Acidjeremy07/Monitoreo-Ambystomas-Arduino/Datasheet's/Referencia esp01.png

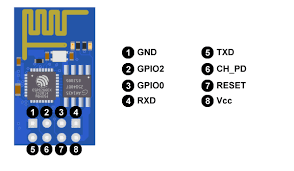
Datasheet's/Referencia esp01.png
