Acidjeremy07/Monitoreo-Ambystomas-Arduino/Expo TT1/Imagenes objetivos especificos/Gabinete de arduino.webp

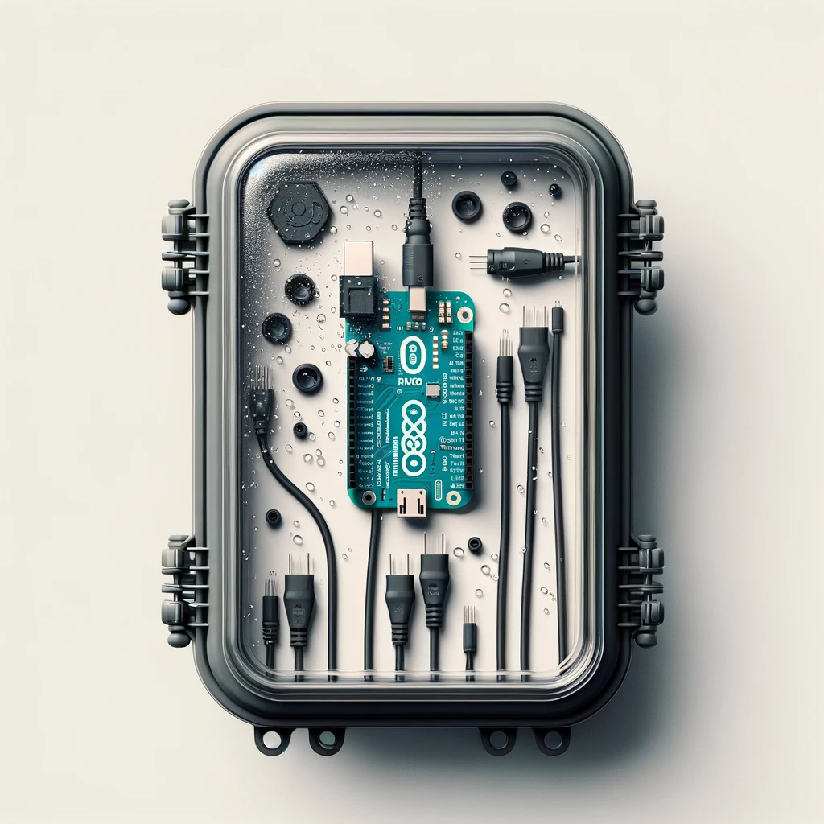
Expo TT1/Imagenes objetivos especificos/Gabinete de arduino.webp
