Acidjeremy07/Monitoreo-Ambystomas-Arduino/Expo TT1/Imagenes objetivos especificos/Sistema de alerta de ajolotes.jpg

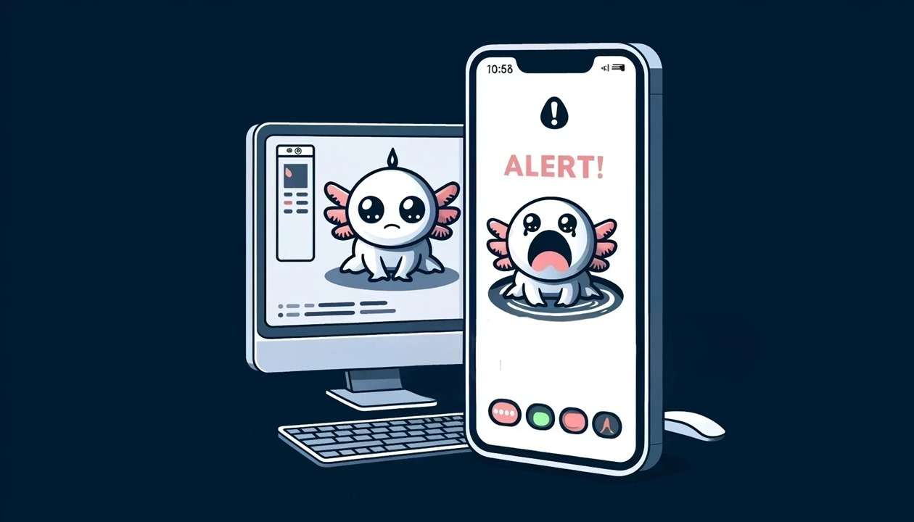
Expo TT1/Imagenes objetivos especificos/Sistema de alerta de ajolotes.jpg
