Acidjeremy07/Monitoreo-Ambystomas-Arduino/Expo TT1/Imagenes objetivos especificos/Sistema web progresivo.webp

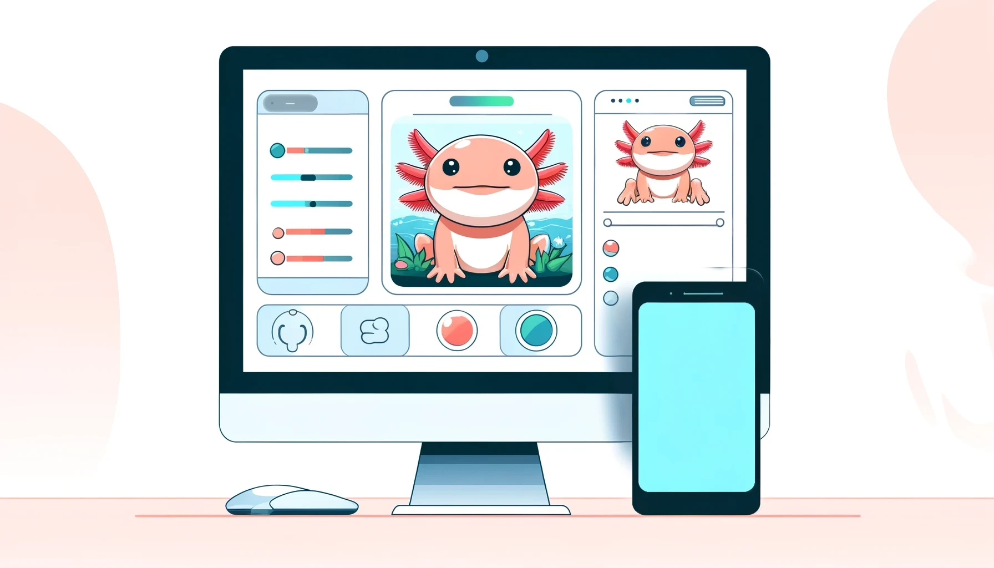
Expo TT1/Imagenes objetivos especificos/Sistema web progresivo.webp
