Acidjeremy07/Monitoreo-Ambystomas-Arduino/Expo TT1/PNG Ajolotes/Ajolotes a la derecha.png

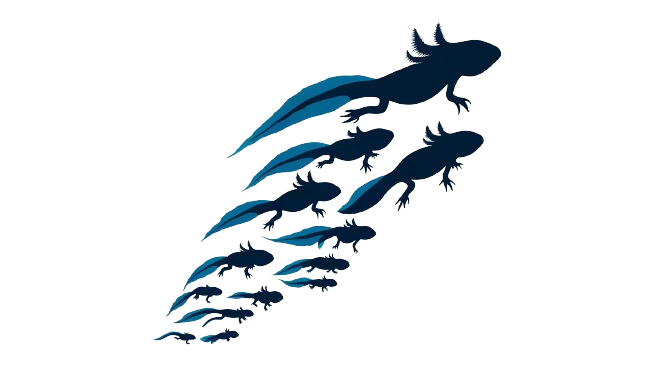
Expo TT1/PNG Ajolotes/Ajolotes a la derecha.png
