Acidjeremy07/Monitoreo-Ambystomas-Arduino/Expo TT1/PNG Ajolotes/Ajolotes bebé.png

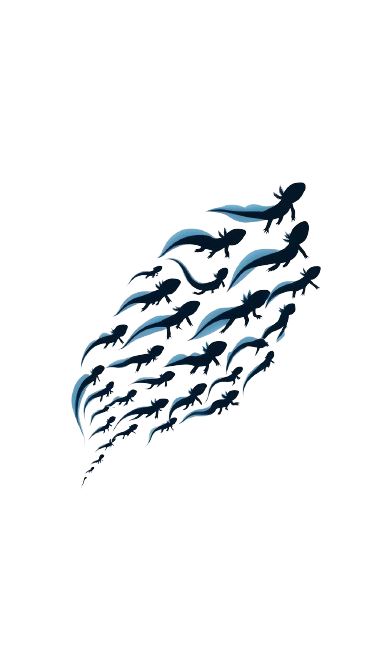
Expo TT1/PNG Ajolotes/Ajolotes bebé.png
