Acidjeremy07/Monitoreo-Ambystomas-Arduino/Expo TT1/PNG Ajolotes/Ajolotes grandes.png

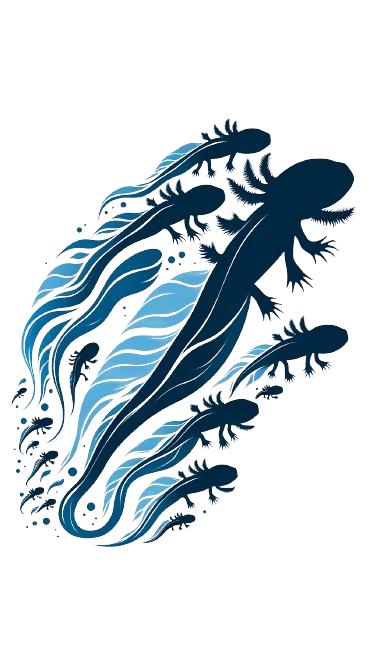
Expo TT1/PNG Ajolotes/Ajolotes grandes.png
