Acidjeremy07/Monitoreo-Ambystomas-Arduino/Expo TT1/PNG Ajolotes/Ajolotes viendo izq.png

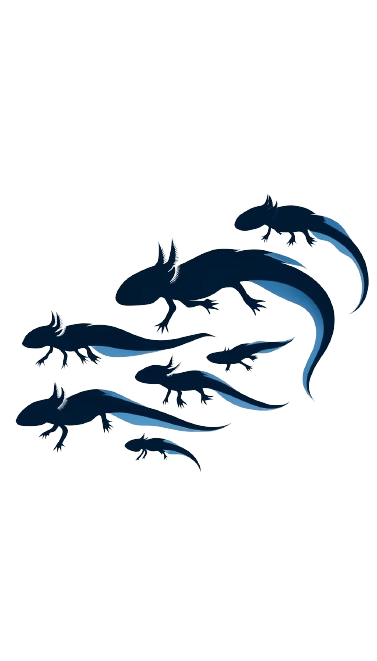
Expo TT1/PNG Ajolotes/Ajolotes viendo izq.png
