Acidjeremy07/Monitoreo-Ambystomas-Arduino/Expo TT1/PNG Ajolotes/Pecera de ajolotes PNG.png

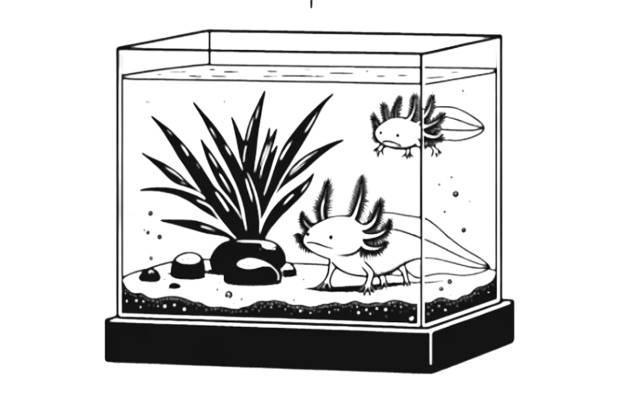
Expo TT1/PNG Ajolotes/Pecera de ajolotes PNG.png
