Acidjeremy07/Monitoreo-Ambystomas-Arduino/Expo TT1/PNG Ajolotes/Varios ajolotes.png

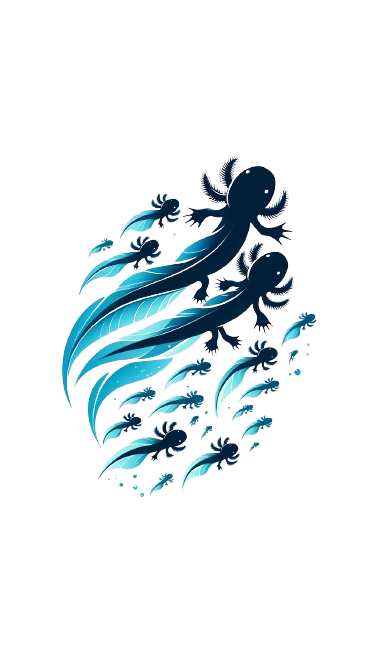
Expo TT1/PNG Ajolotes/Varios ajolotes.png
