Acidjeremy07/Monitoreo-Ambystomas-Arduino/PCB/TT Ambystoma v10 w-logo.PDF

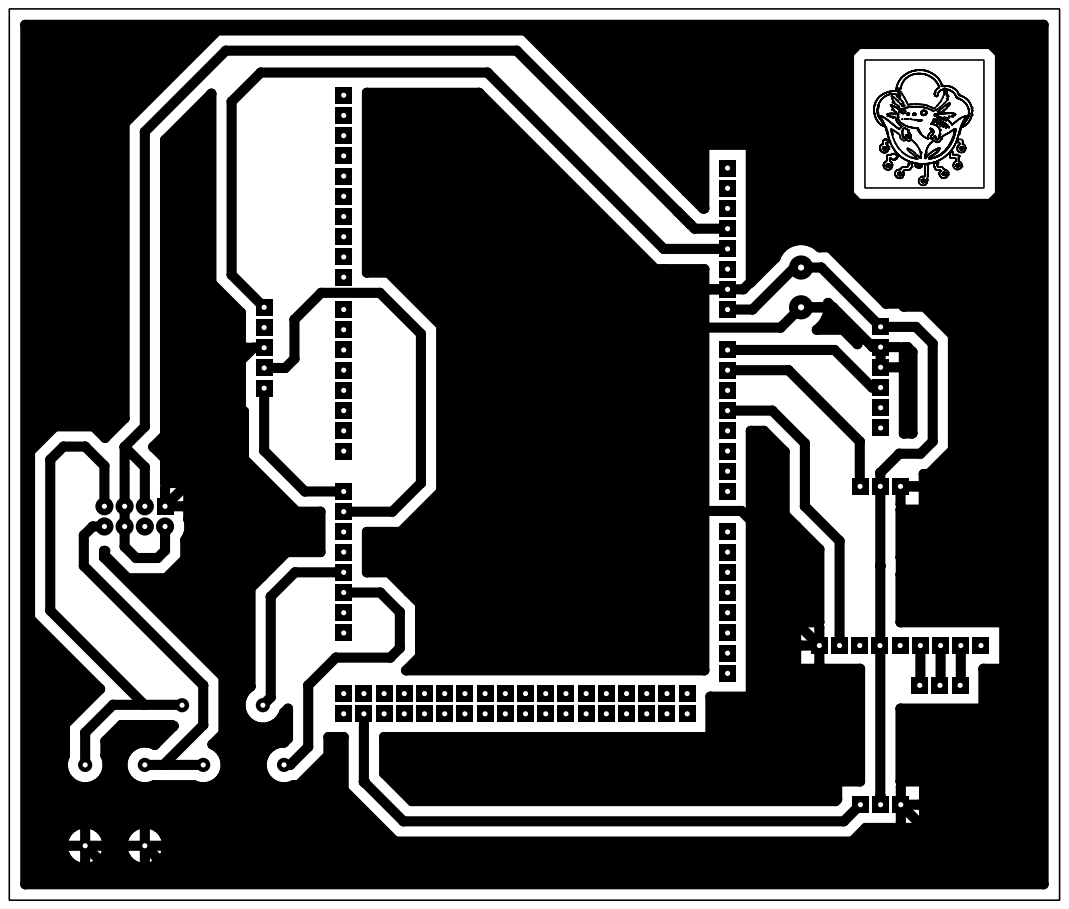
[picture p62: page 1]
