Acidjeremy07/Monitoreo-Ambystomas-Arduino/PCB/TT Ambystoma v5 w-logo imprimir varios.PDF

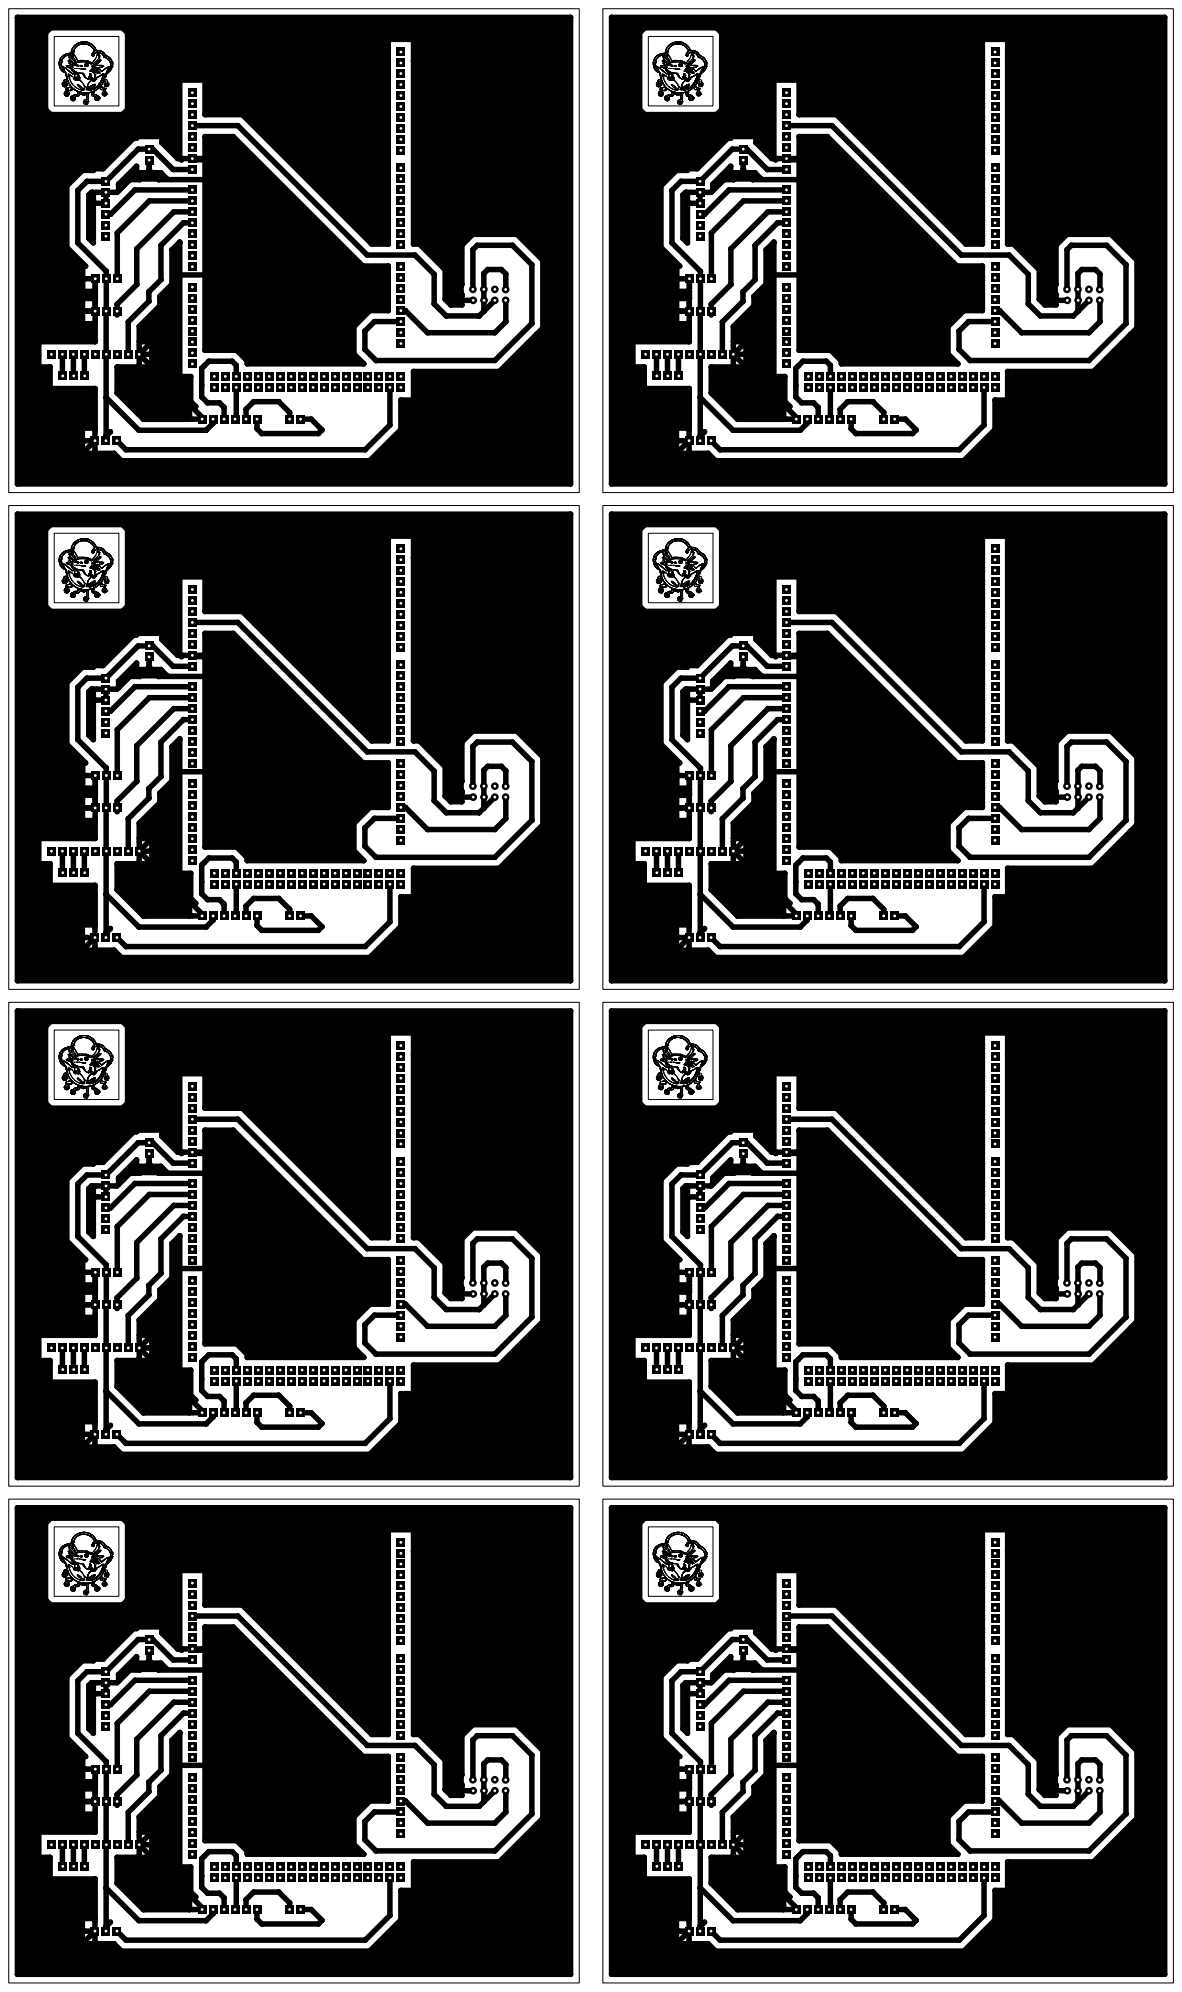
[picture p63: page 1]
