Acidjeremy07/Monitoreo-Ambystomas-Arduino/PCB/PDF imprimir/TT Ambystoma v3.2 w-logo.PDF

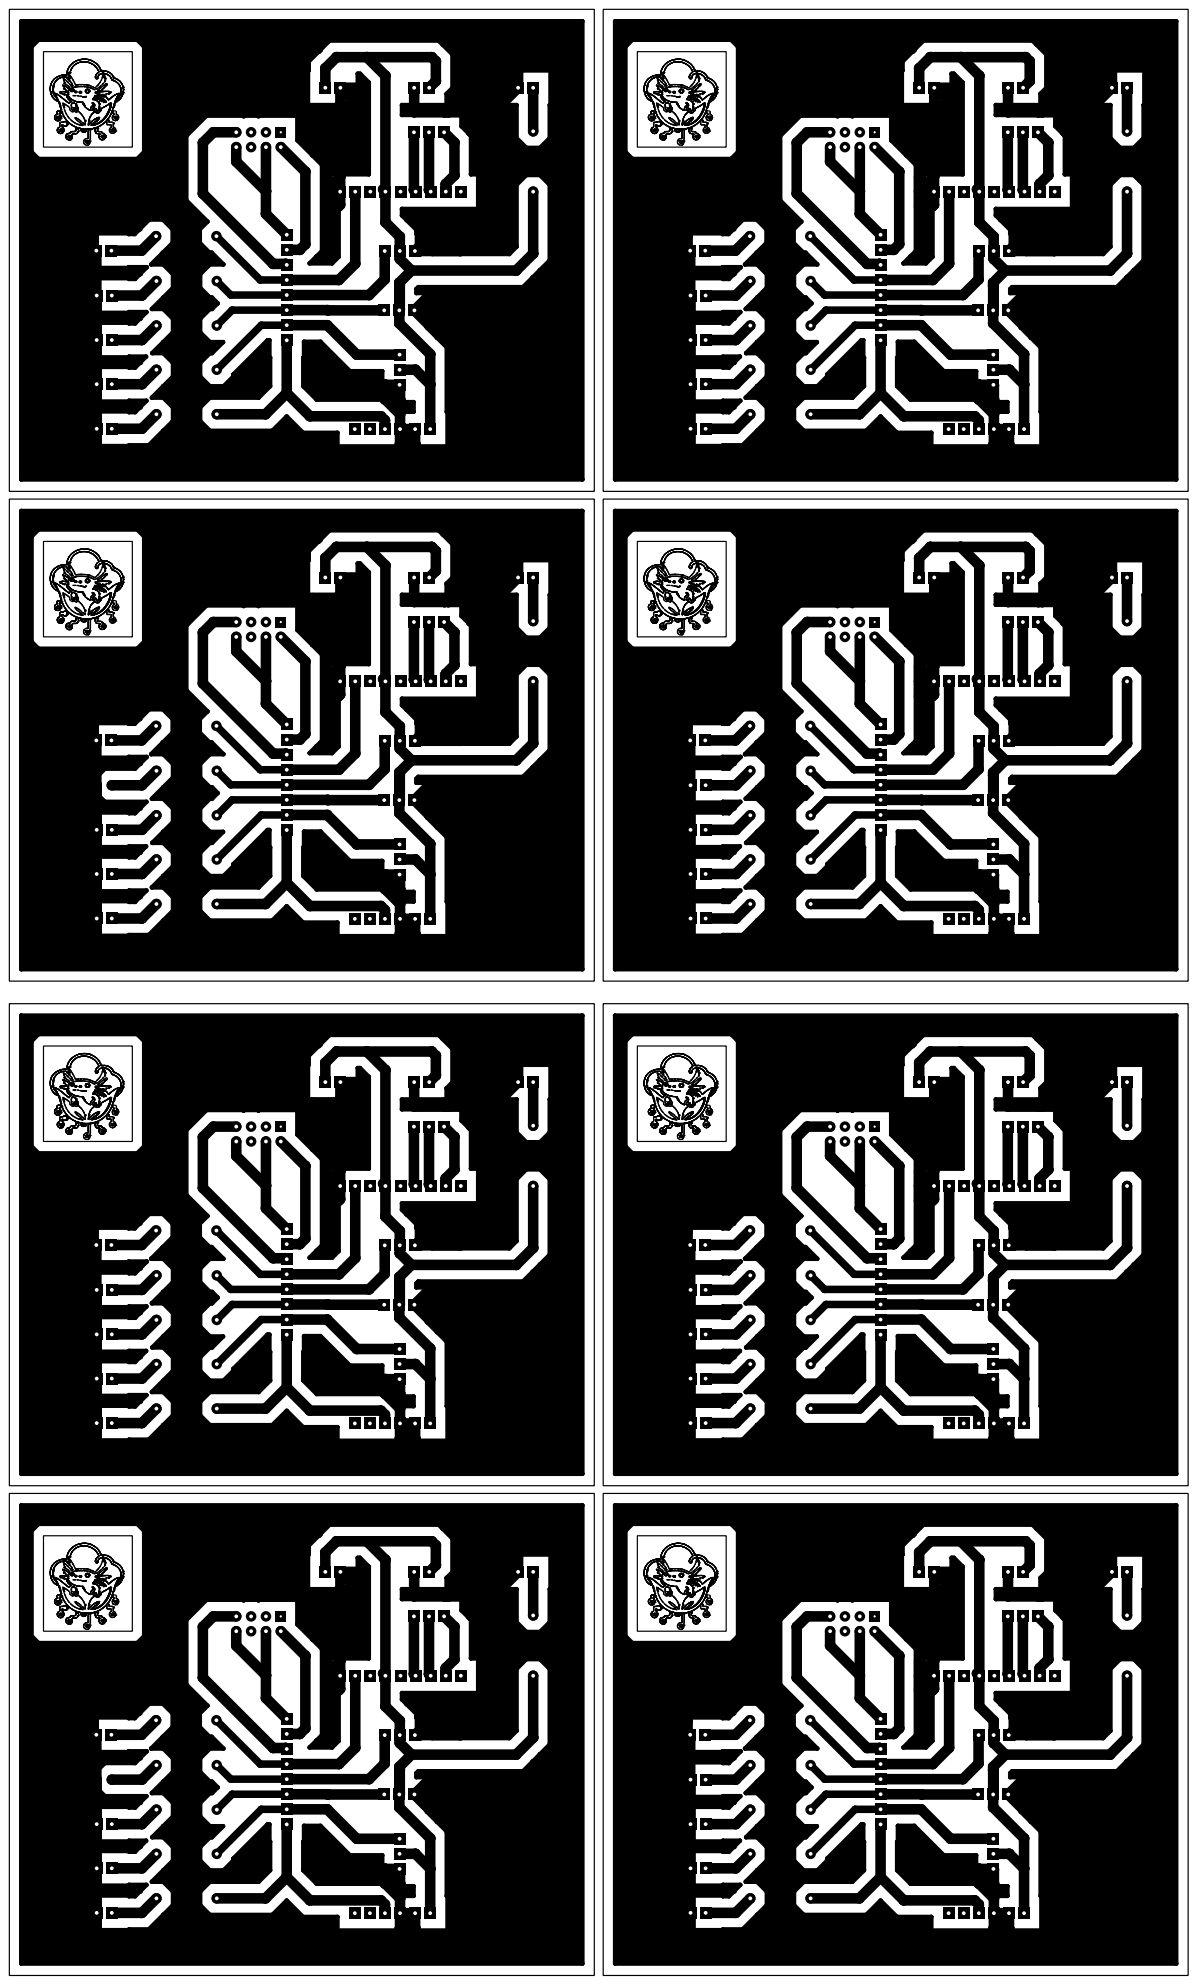
[picture p64: page 1]
