Acidjeremy07/Monitoreo-Ambystomas-Arduino/PCB/PDF imprimir/TT Ambystoma v3.PDF

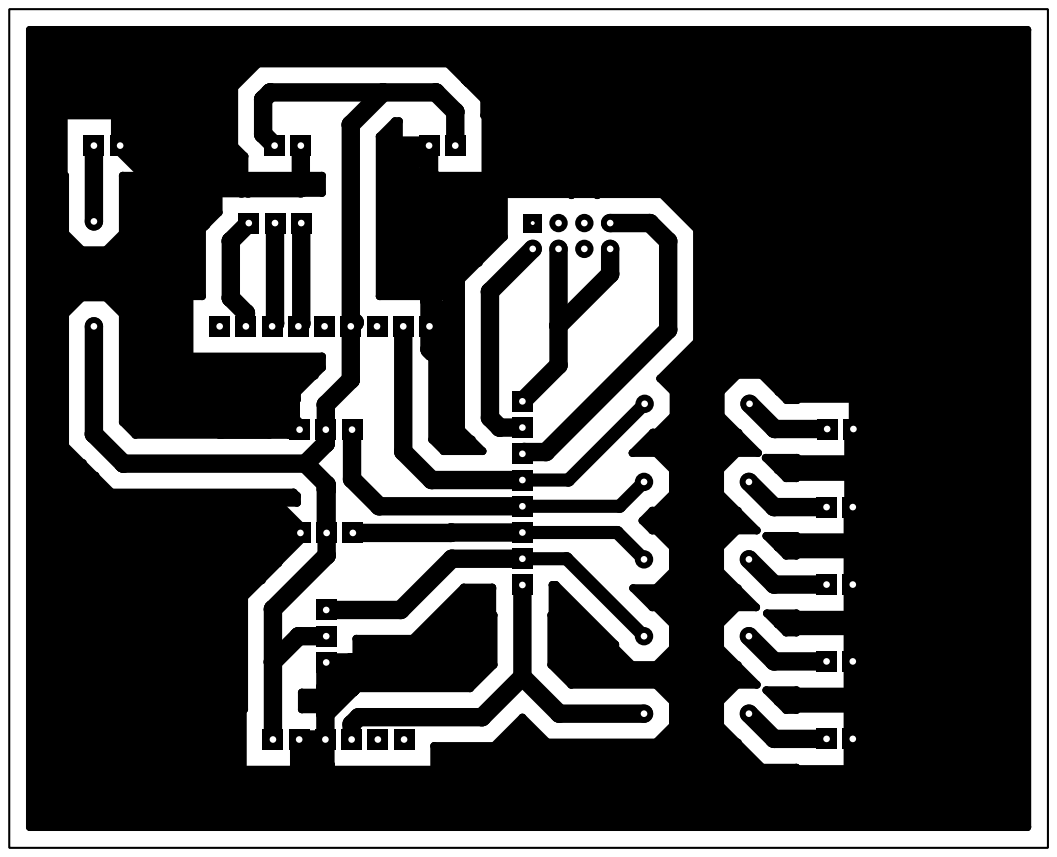
[picture p65: page 1]
