Acidjeremy07/Monitoreo-Ambystomas-Arduino/PCB/PDF imprimir/TT Ambystoma v2 X.PDF

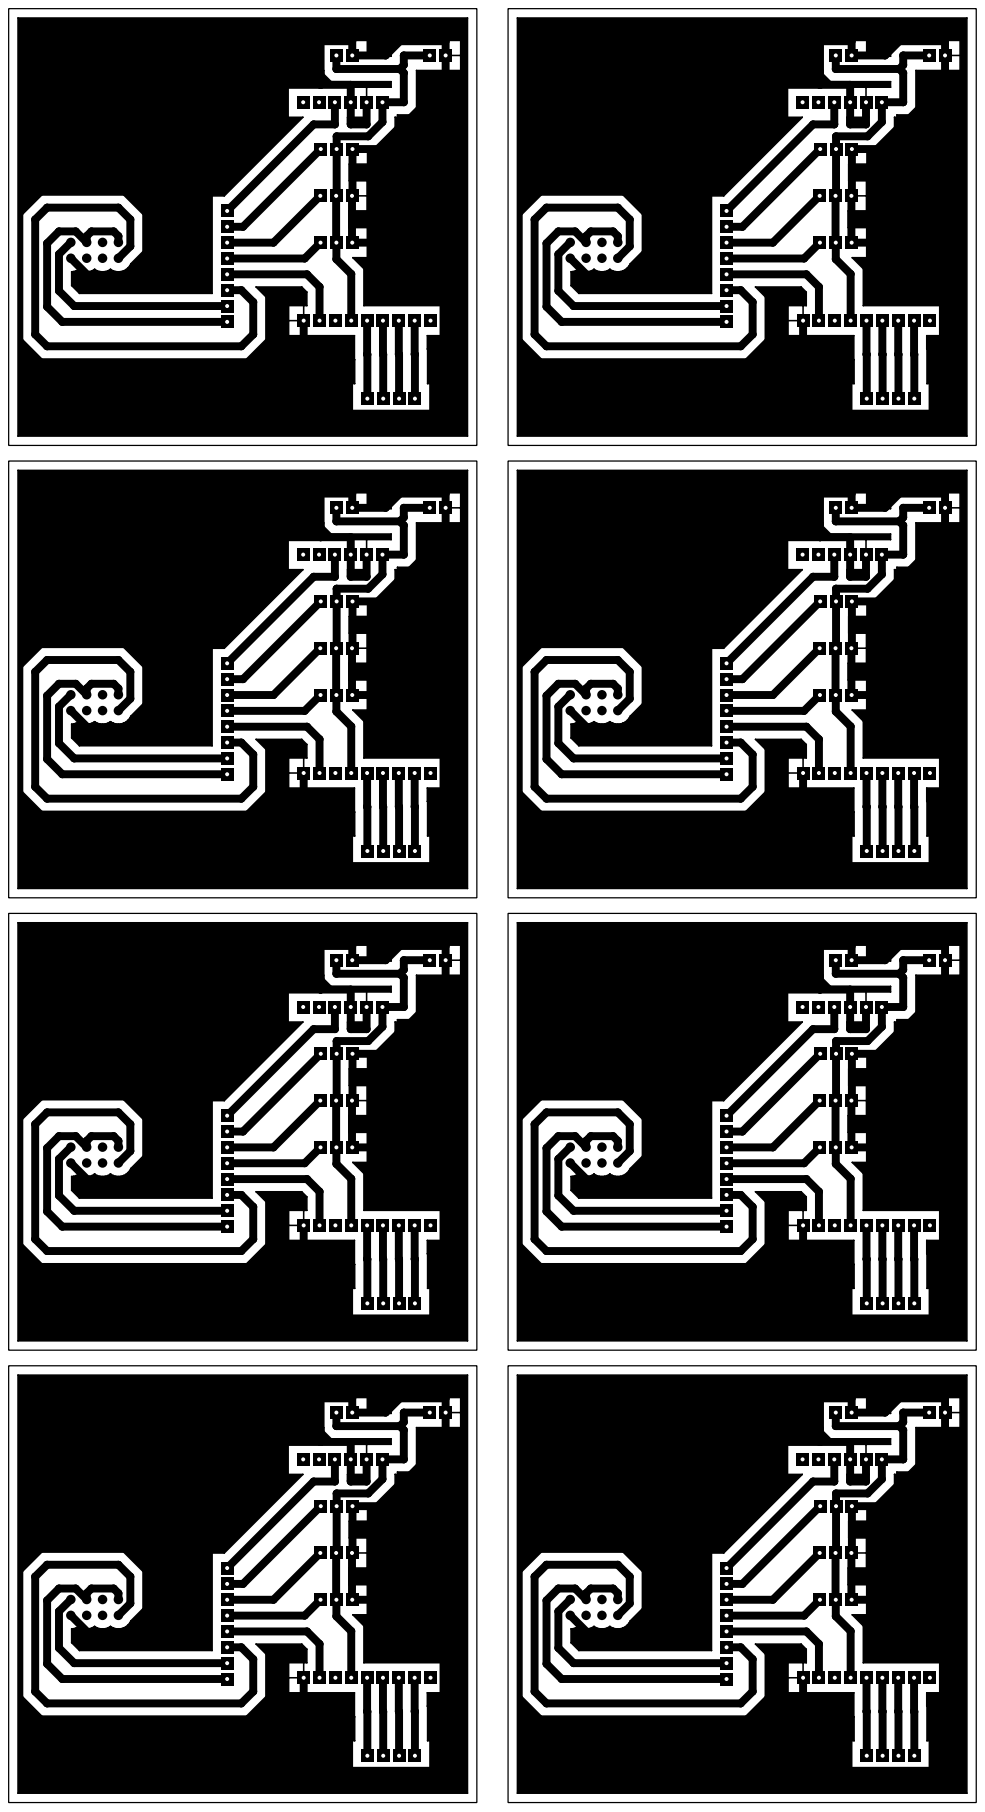
[picture p66: page 1]
