Acidjeremy07/Monitoreo-Ambystomas-Arduino/PCB/tt-v5.PDF

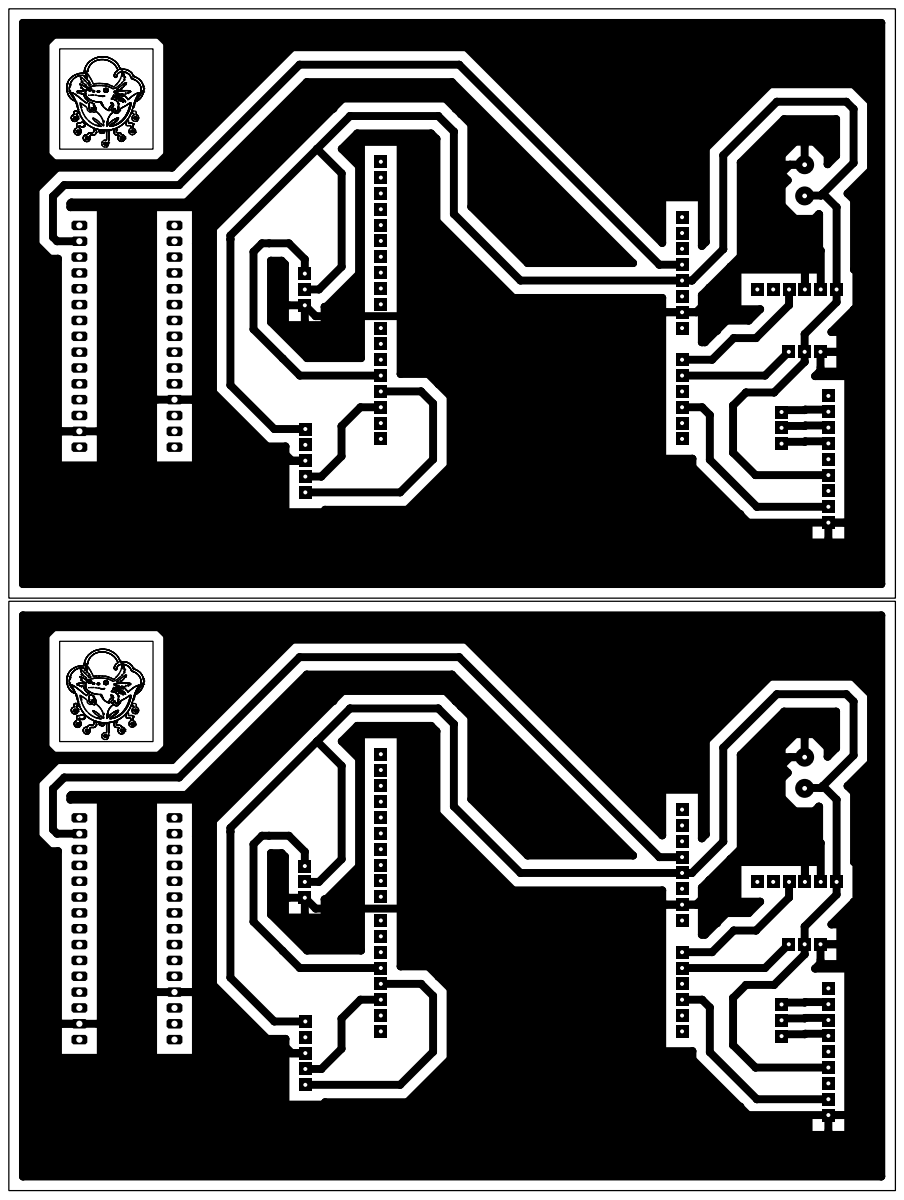
[picture p67: page 1]
