Acidjeremy07/Monitoreo-Ambystomas-Arduino/PCB/TT-V11.PDF

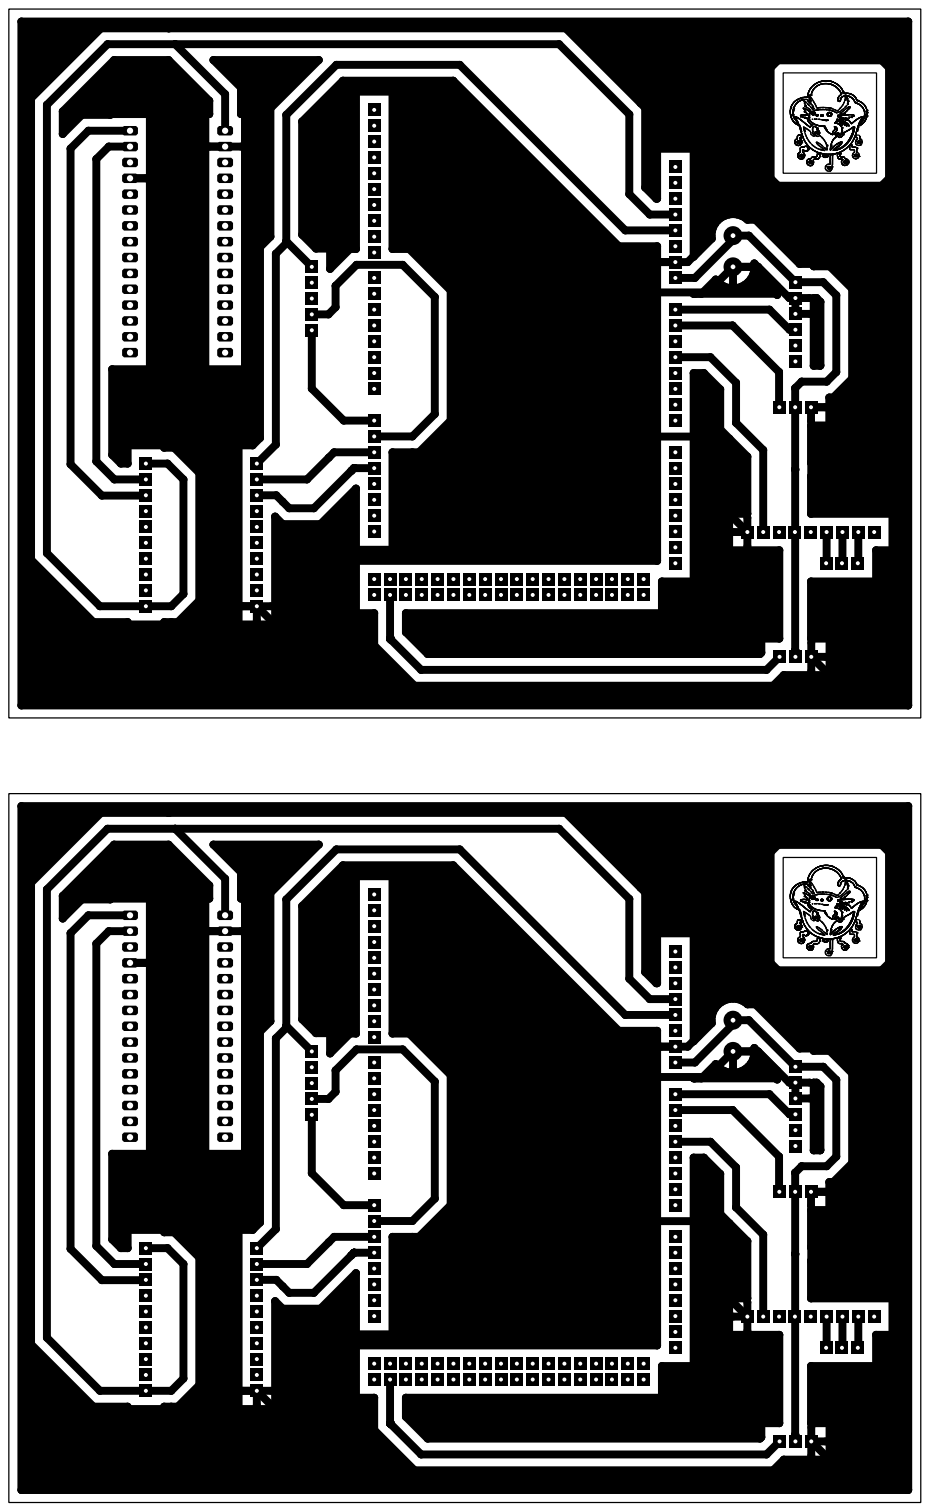
[picture p68: page 1]
