Acidjeremy07/Monitoreo-Ambystomas-Arduino/PCB/tt-v12.PDF

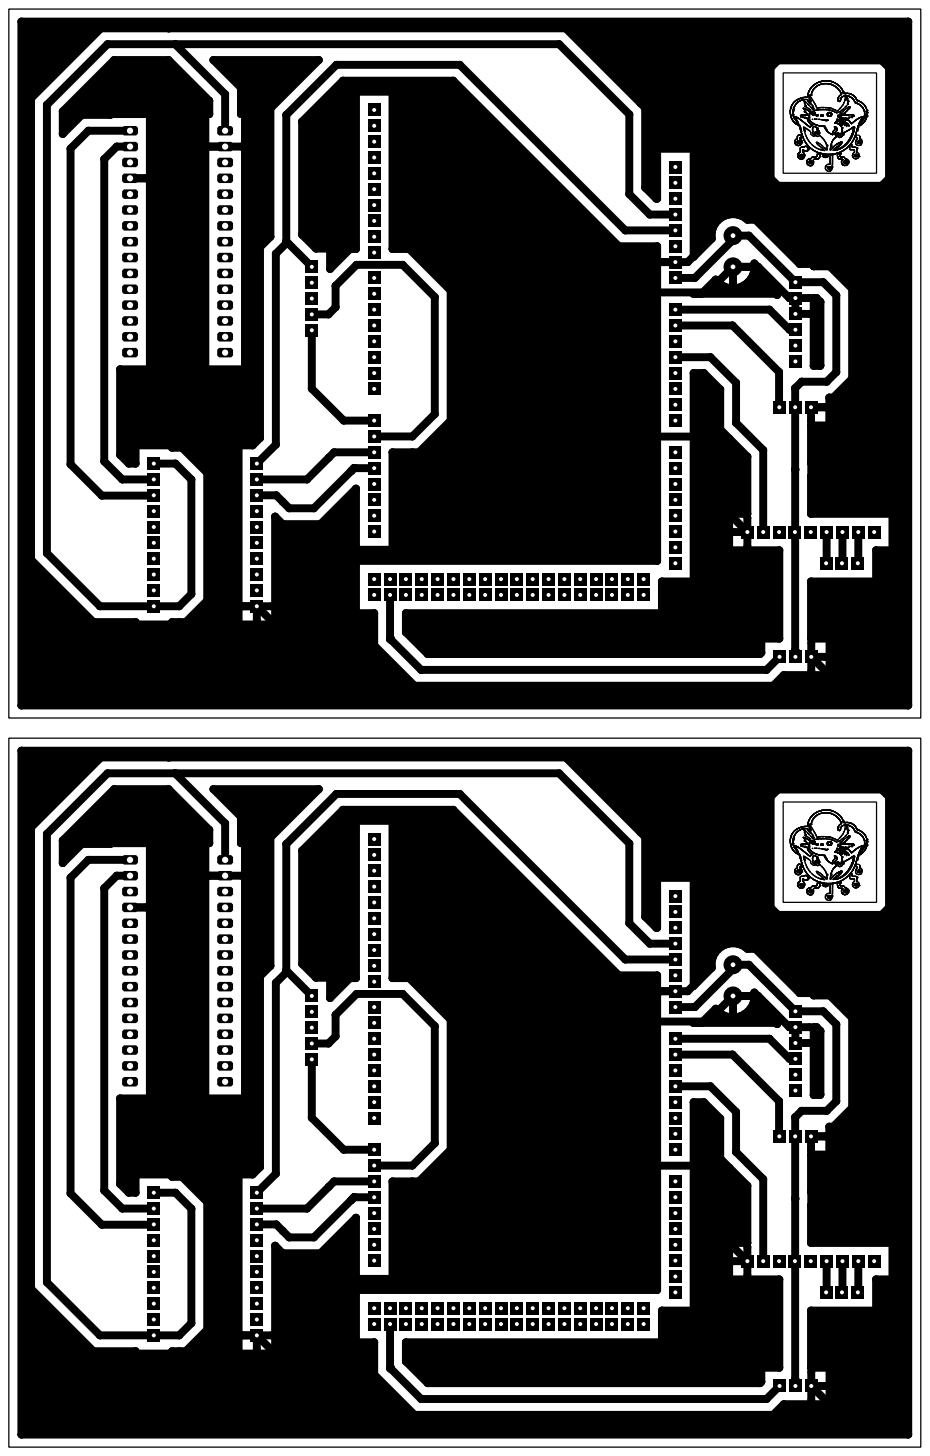
[picture p69: page 1]
