Acidjeremy07/Monitoreo-Ambystomas-Arduino/PCB/tt-v13.PDF

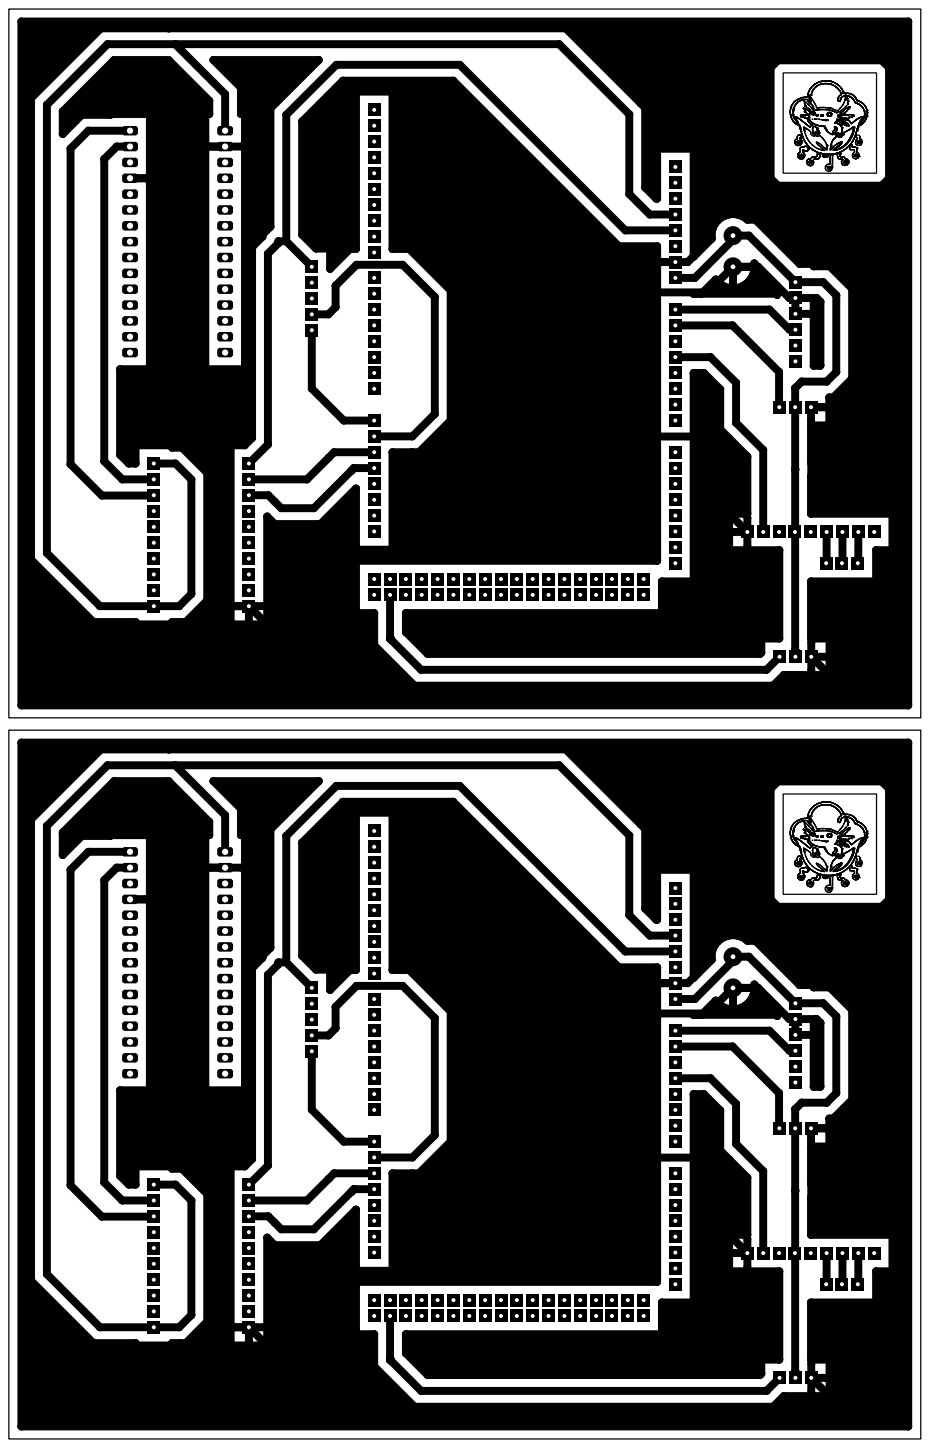
[picture p70: page 1]
