Acidjeremy07/Monitoreo-Ambystomas-Arduino/PCB/TT Ambystoma uno  w-logo.PDF

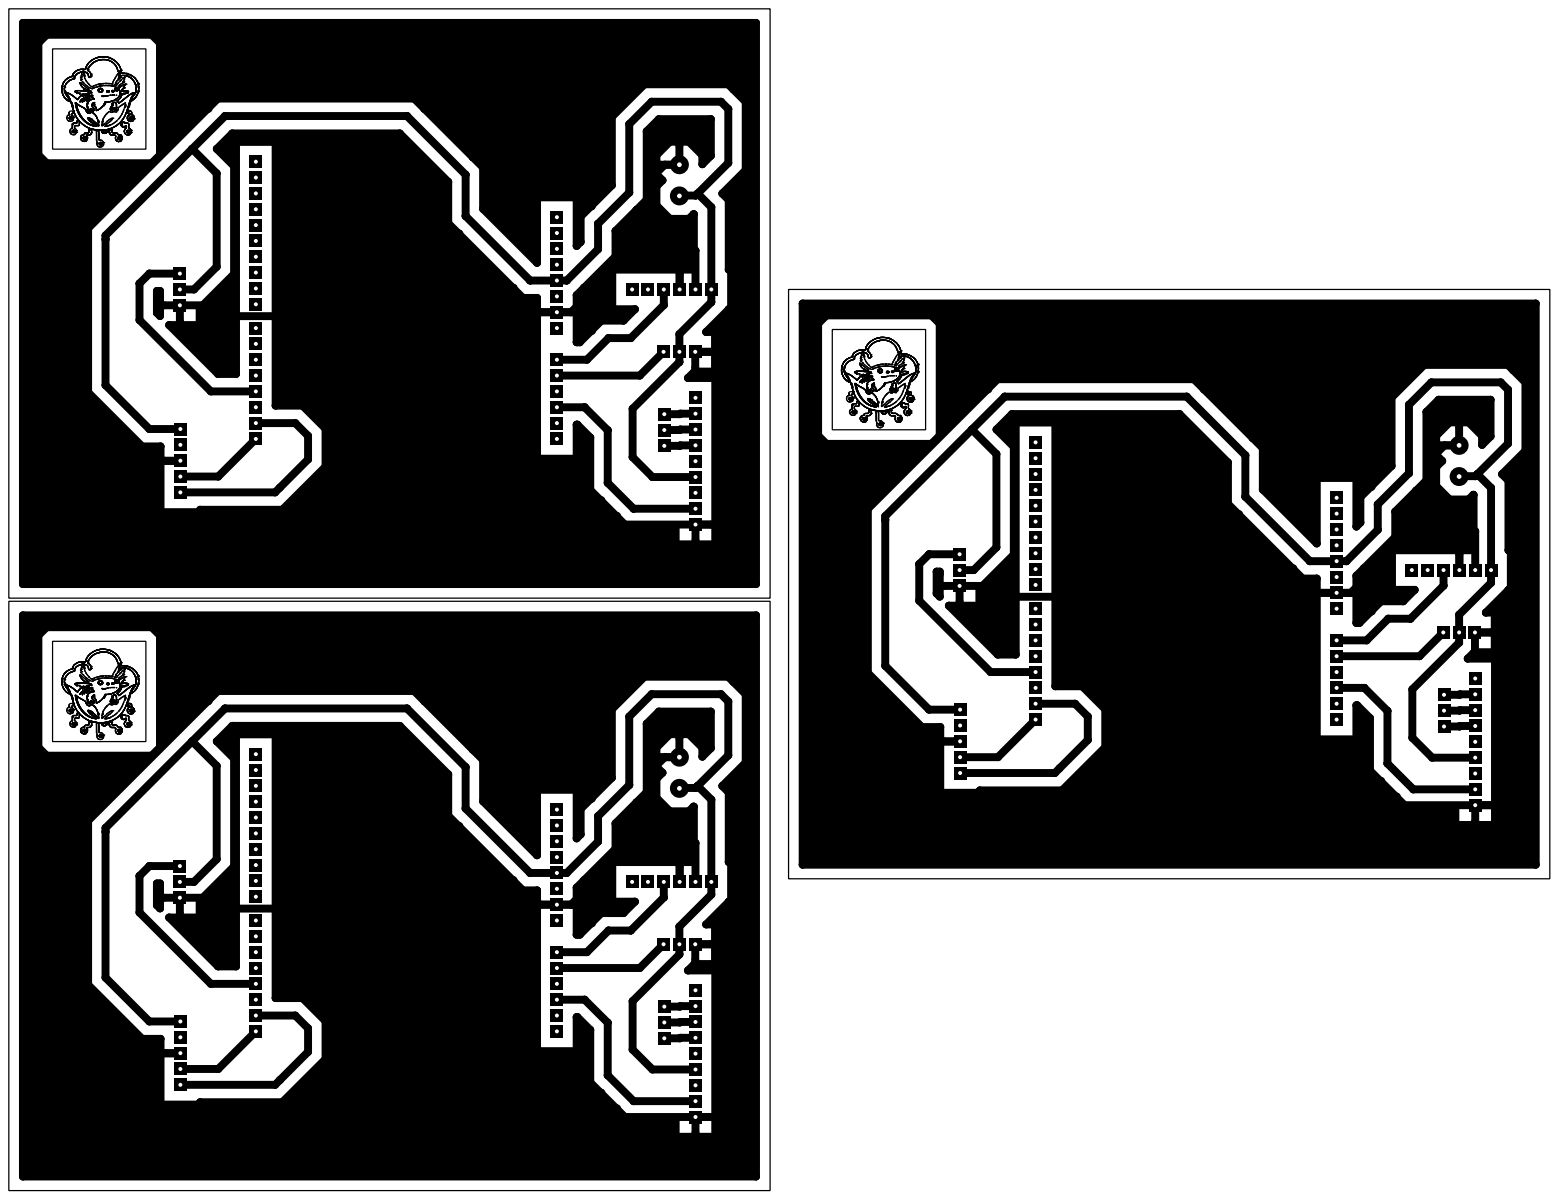
[picture p71: page 1]
