Acidjeremy07/Monitoreo-Ambystomas-Arduino/PCB/tt-v10.PDF

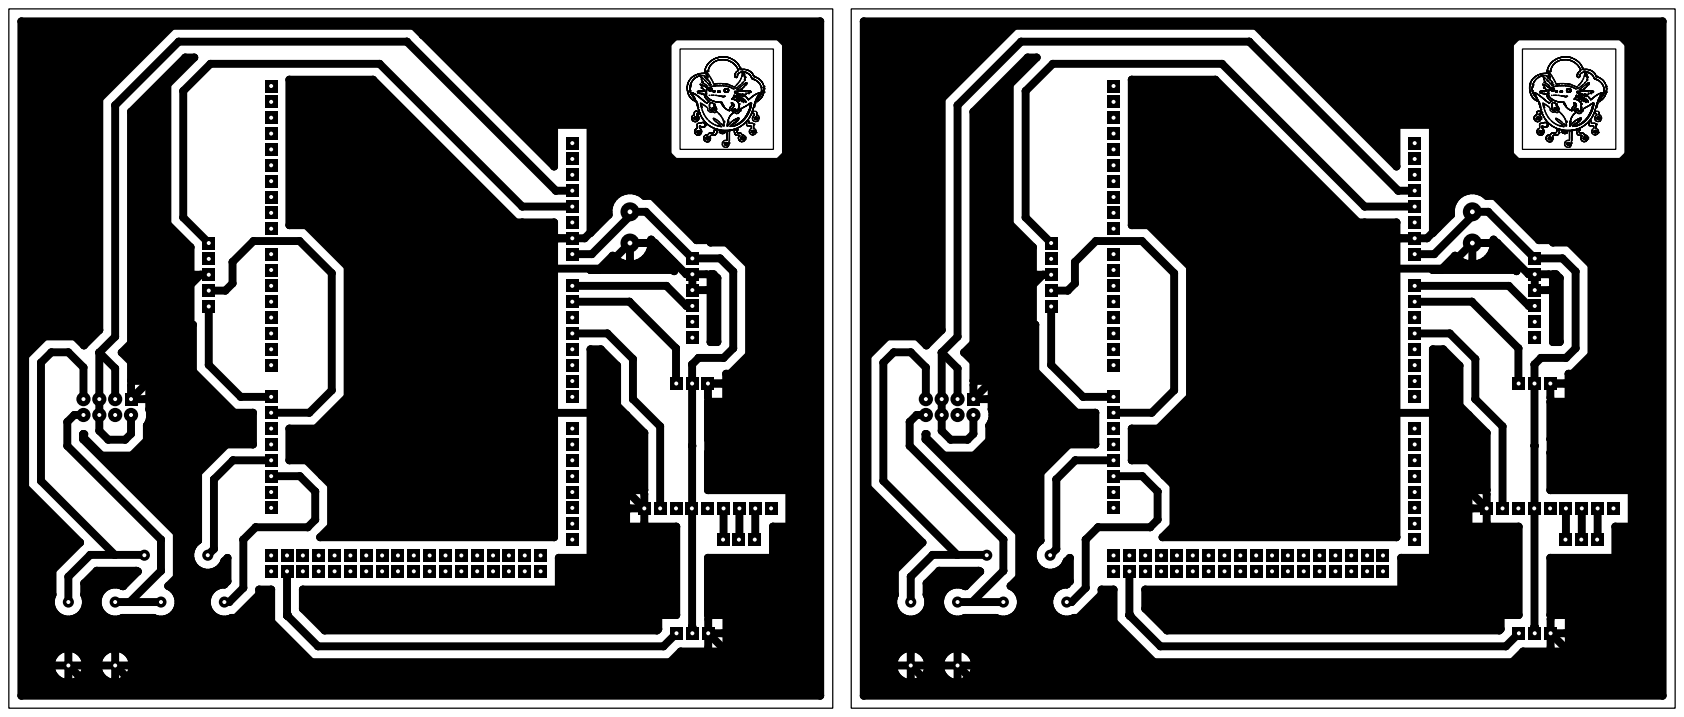
[picture p72: page 1]
