Acidjeremy07/Monitoreo-Ambystomas-Arduino/PCB/TT Ambystoma v8 w-logo.PDF

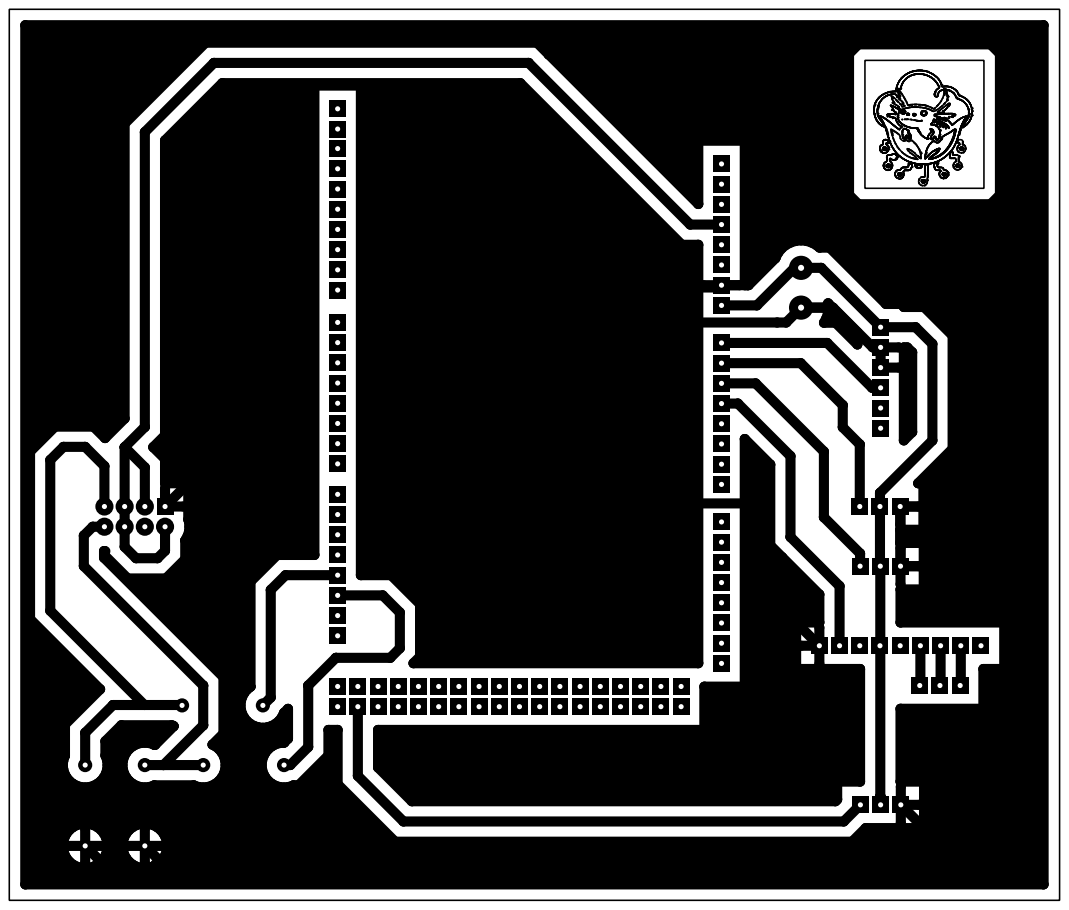
[picture p73: page 1]
