Acidjeremy07/Monitoreo-Ambystomas-Arduino/PCB/TT-V8.PDF

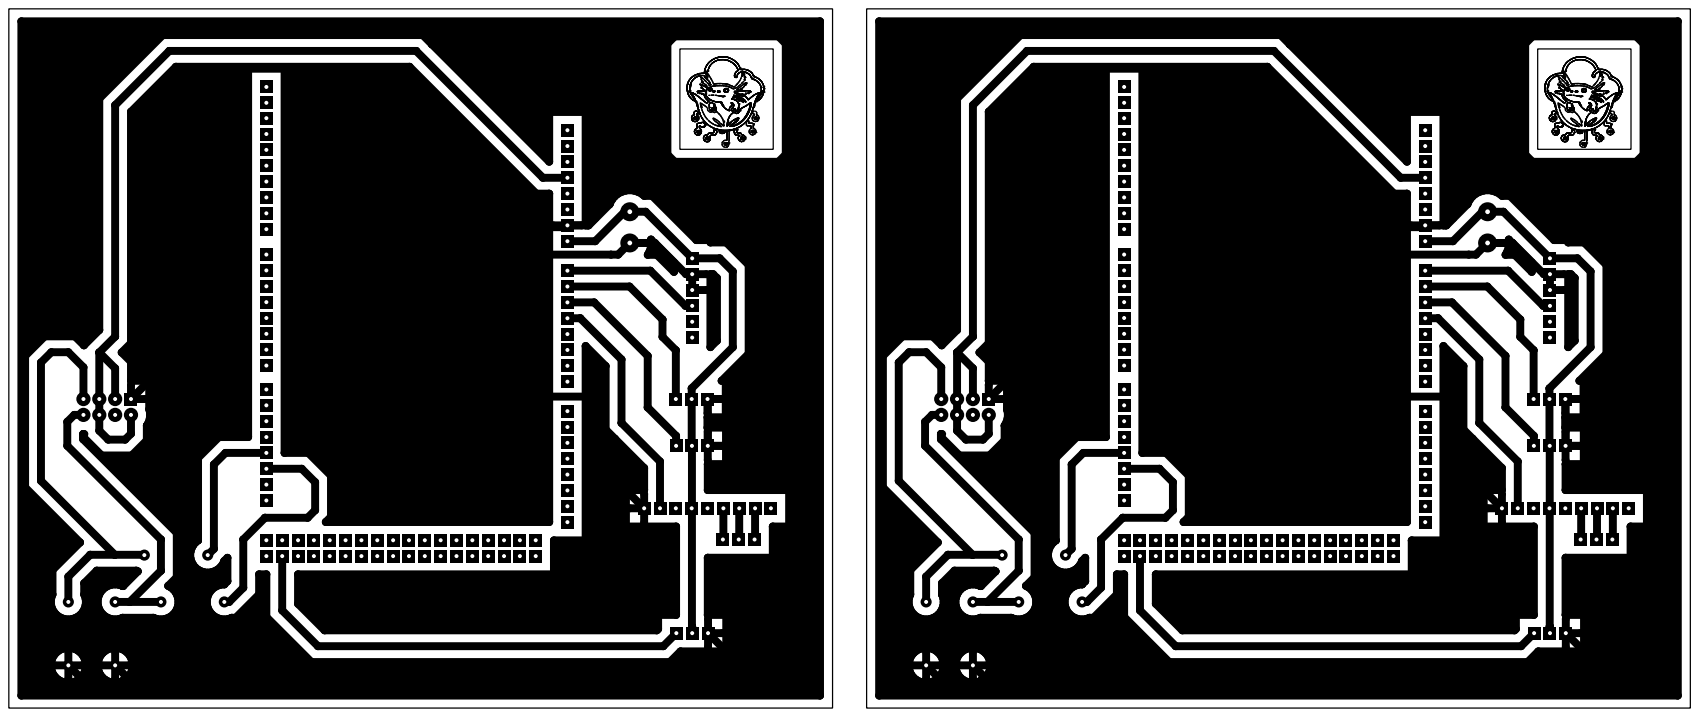
[picture p74: page 1]
