Acidjeremy07/Monitoreo-Ambystomas-Arduino/PCB/tt-v9.PDF

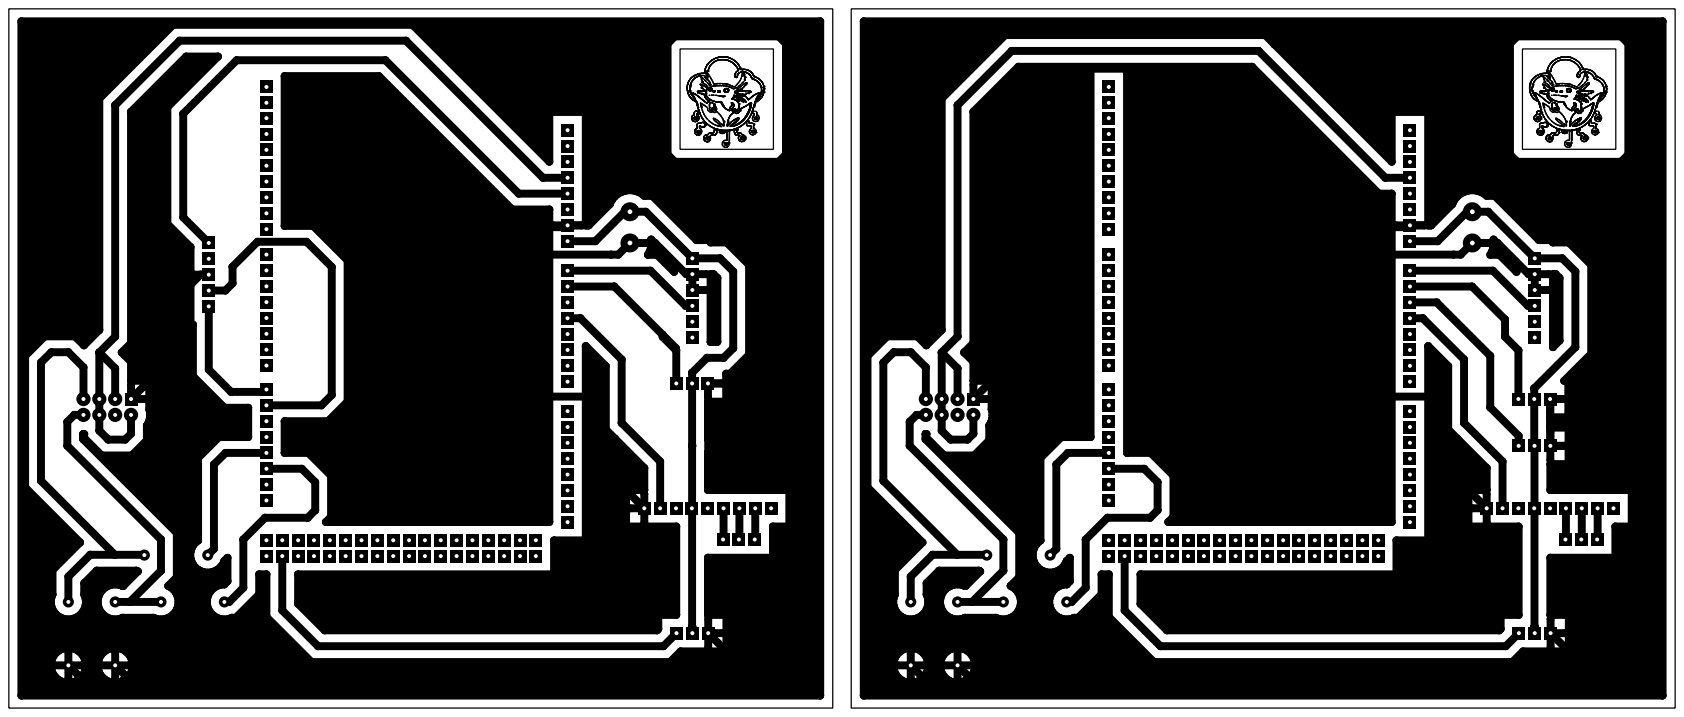
[picture p75: page 1]
