Acidjeremy07/Monitoreo-Ambystomas-Arduino/PCB/TT Ambystoma v4 w-logo imprimir varios.PDF

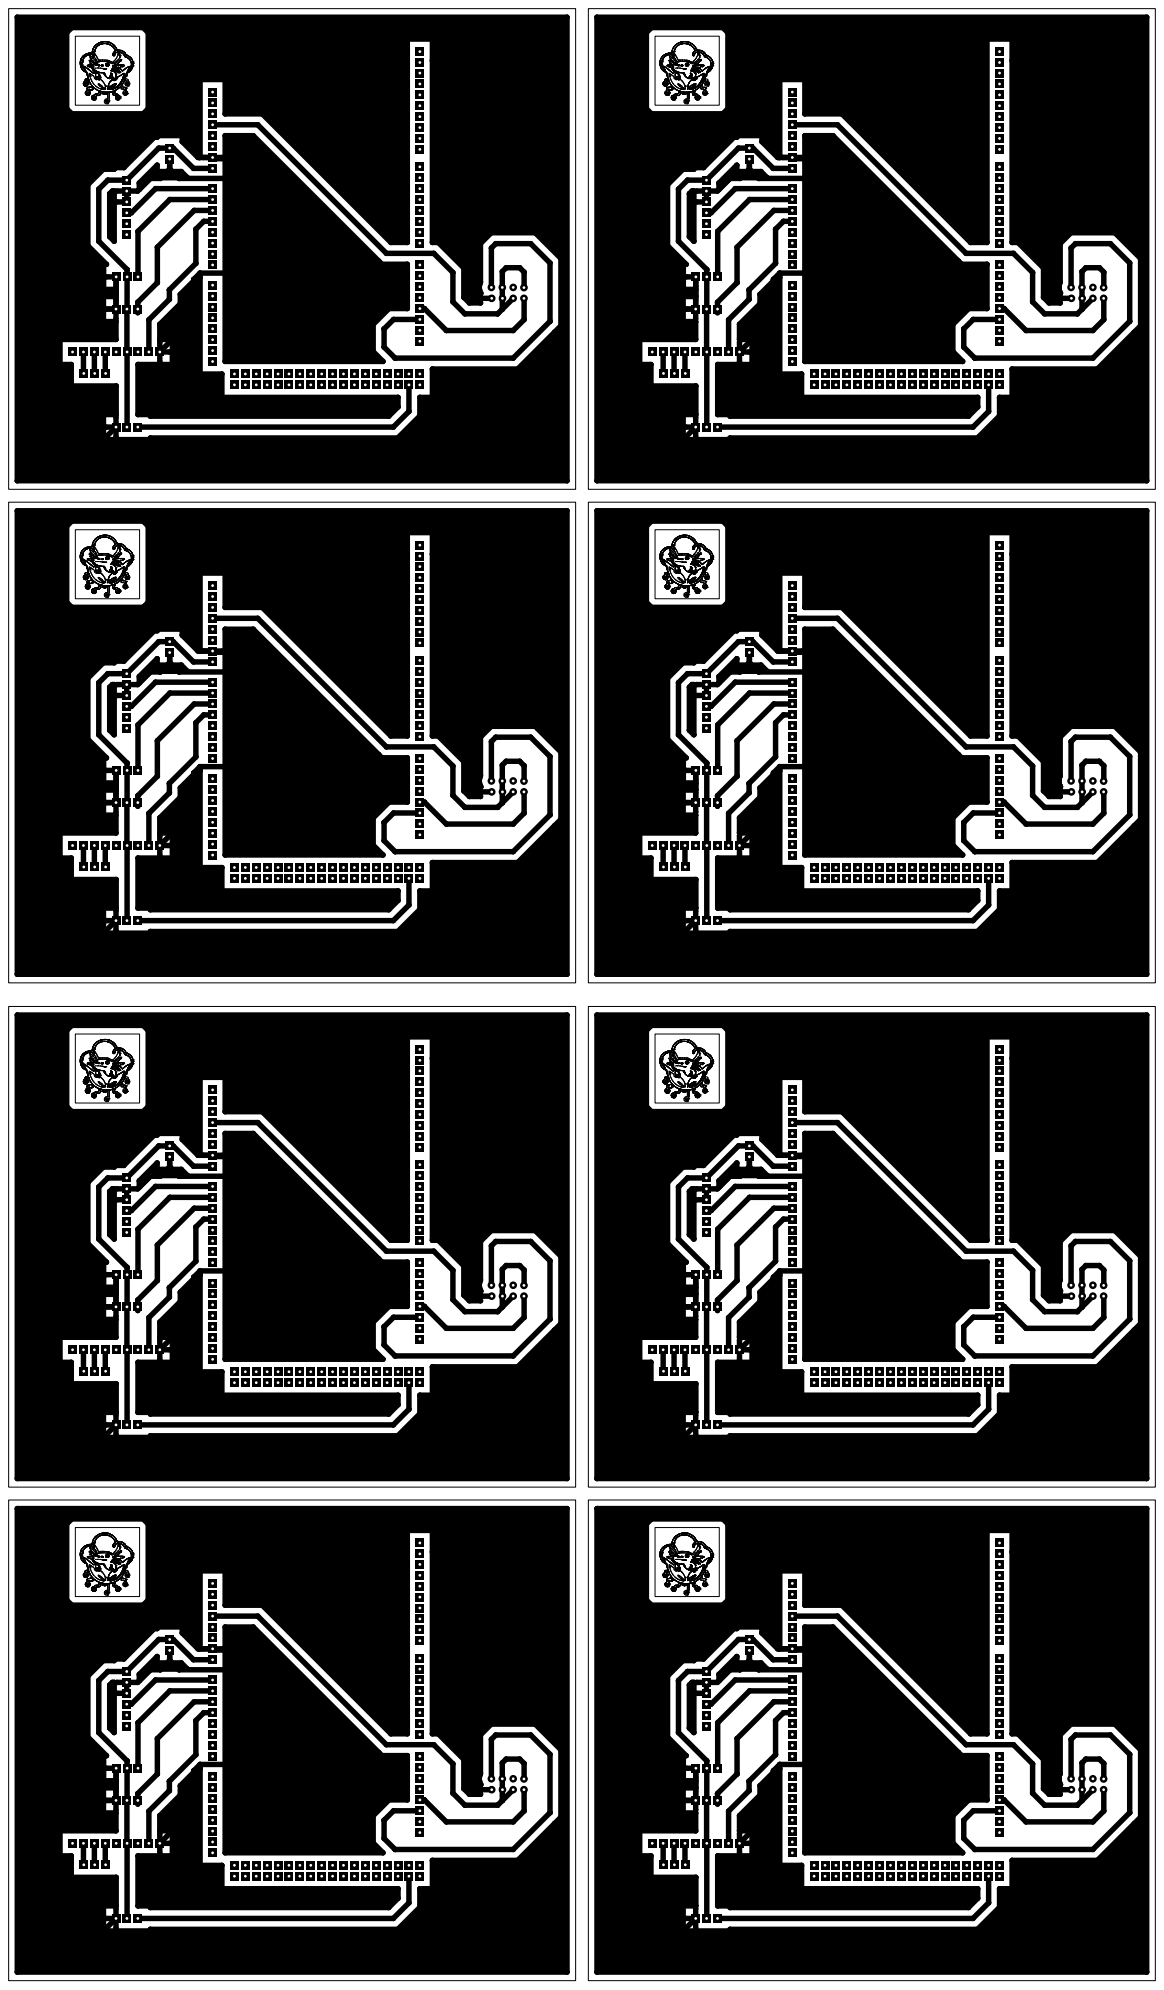
[picture p76: page 1]
