Acidjeremy07/Monitoreo-Ambystomas-Arduino/PCB/TT Ambystoma v4 w-logo.PDF

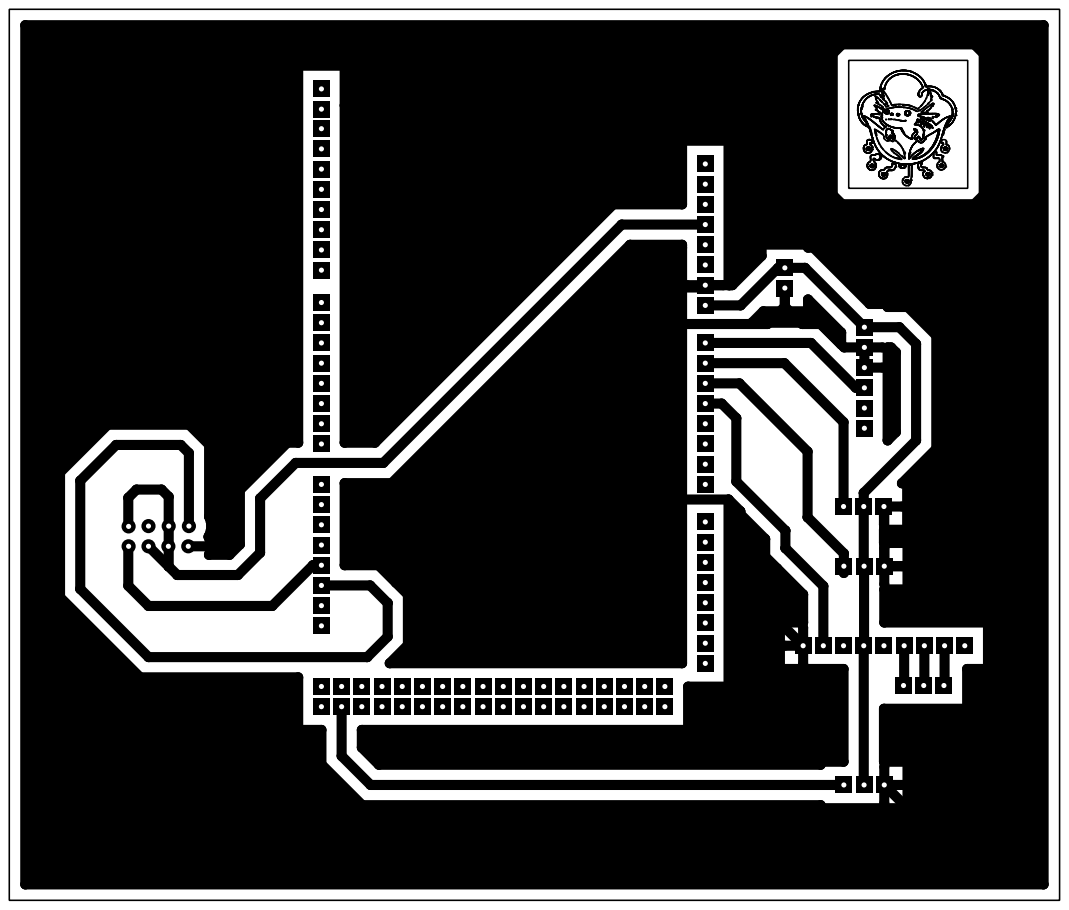
[picture p77: page 1]
