Acidjeremy07/Monitoreo-Ambystomas-Arduino/PCB/TT Ambystoma v6 w-logo.PDF

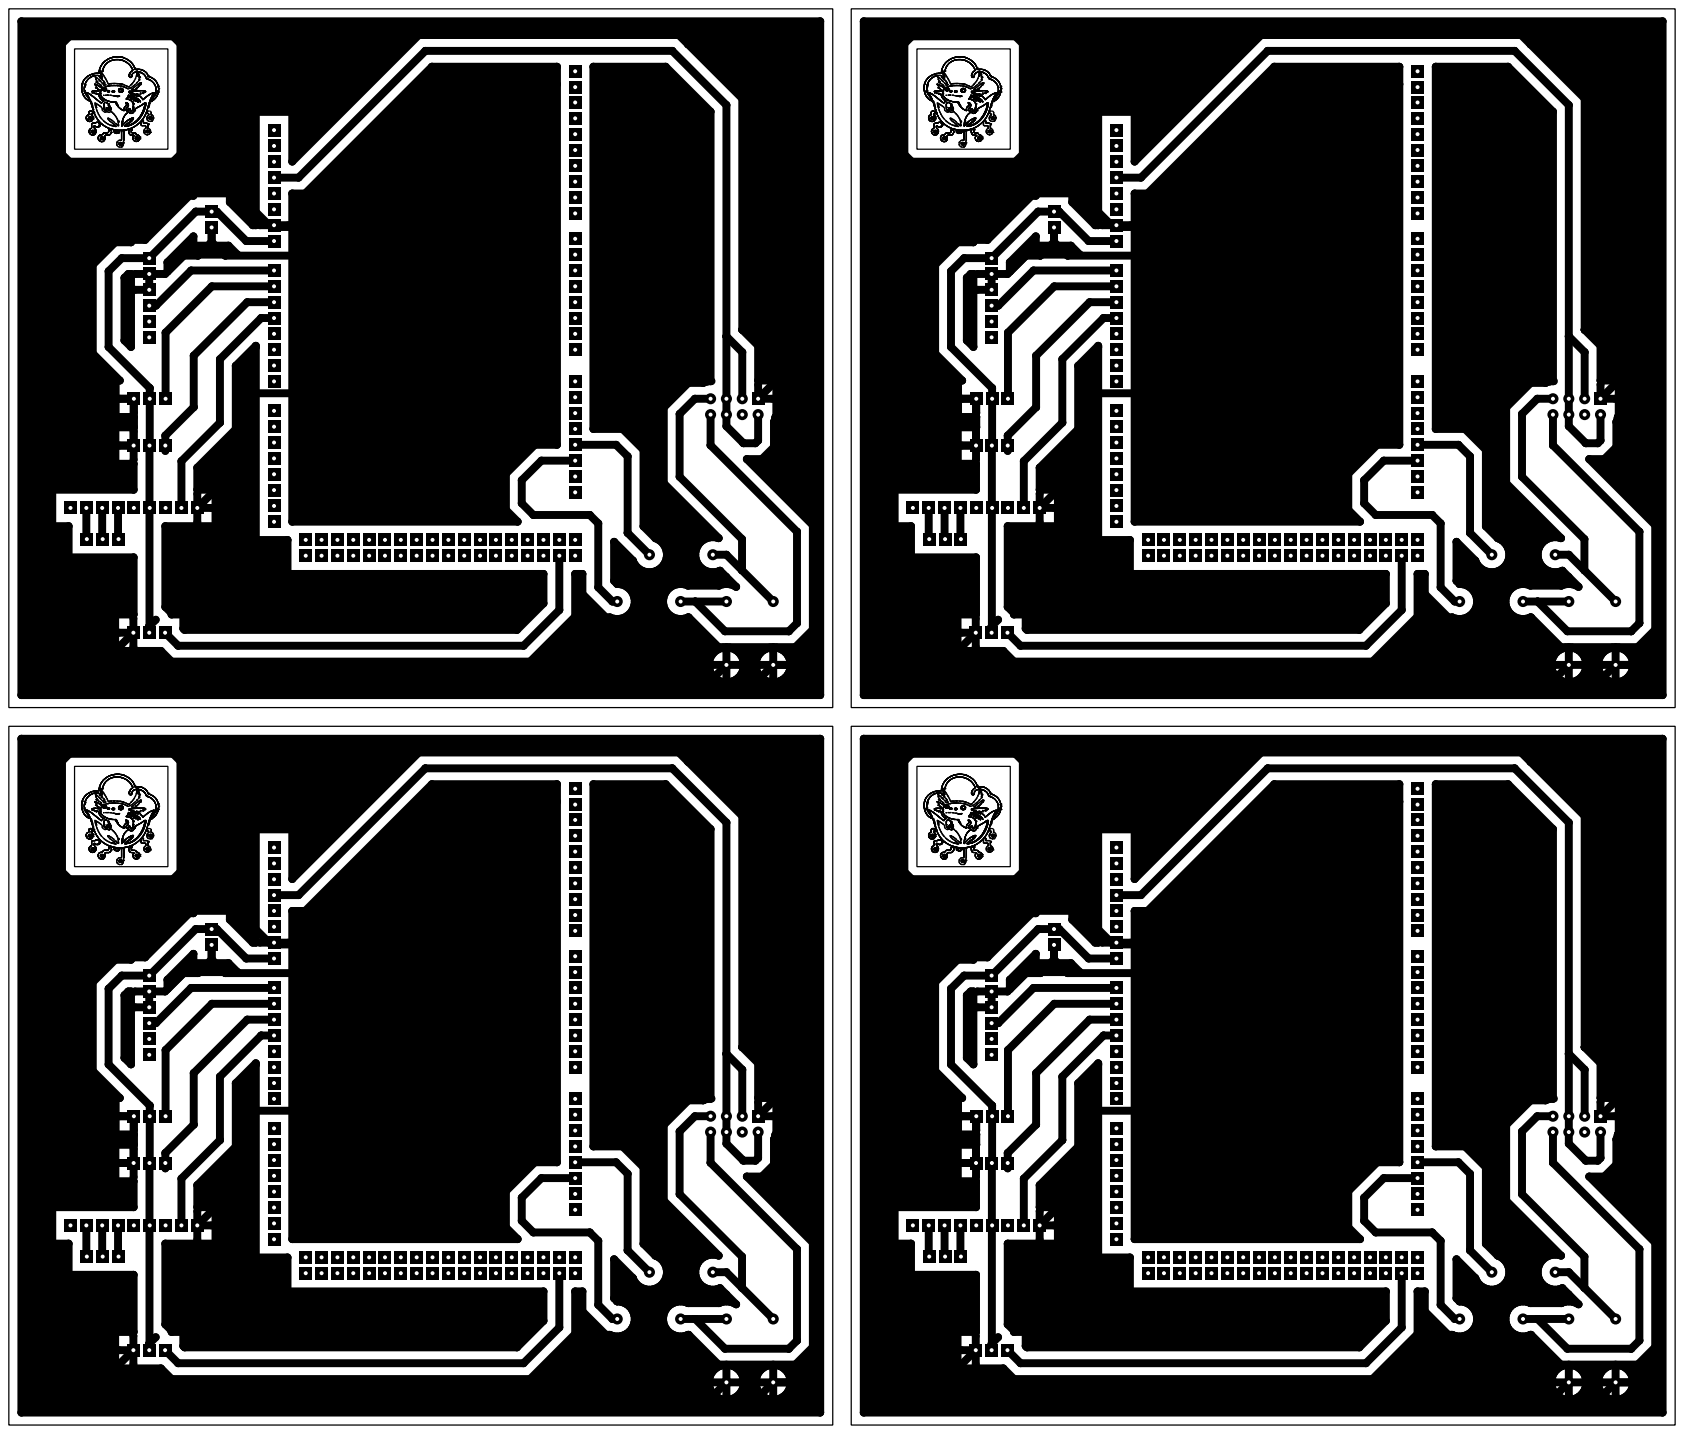
[picture p78: page 1]
