Acidjeremy07/Monitoreo-Ambystomas-Arduino/PCB/TT Ambystoma v7 w-logo.PDF

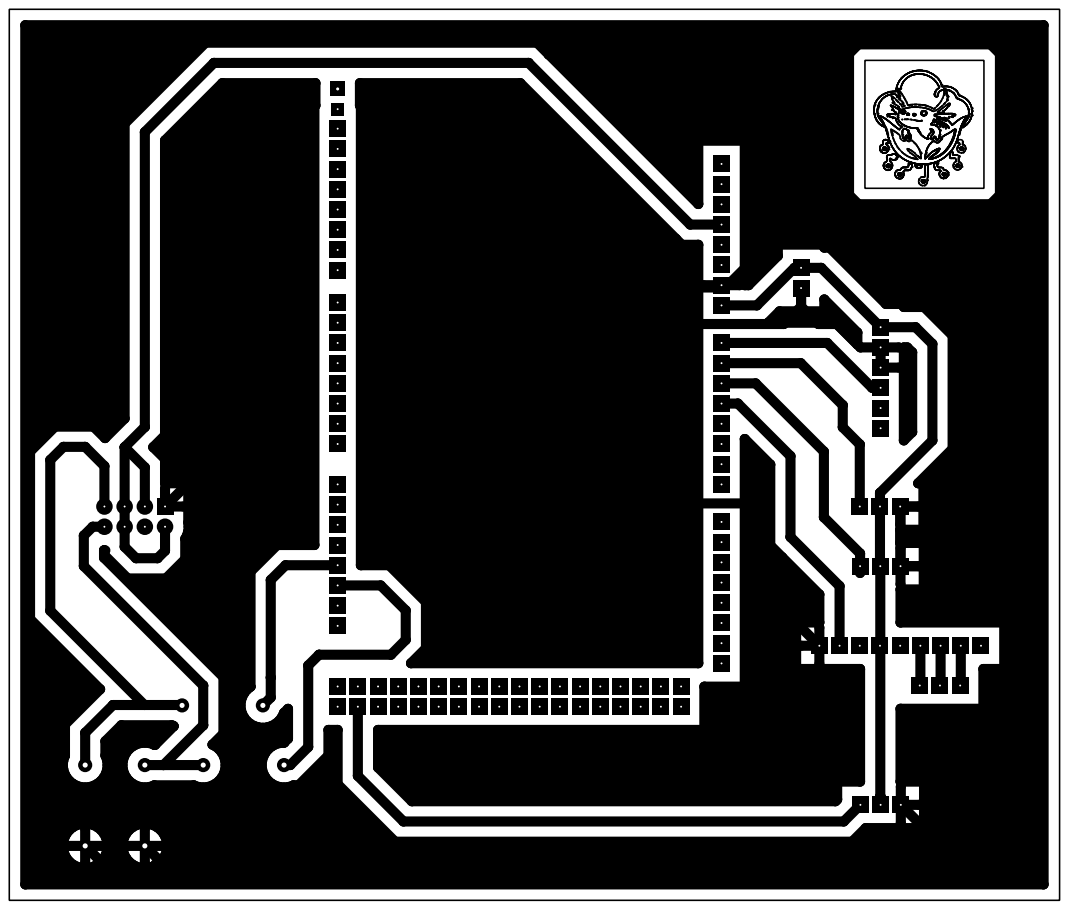
[picture p79: page 1]
