Acidjeremy07/Monitoreo-Ambystomas-Arduino/PCB/tt-v6.PDF

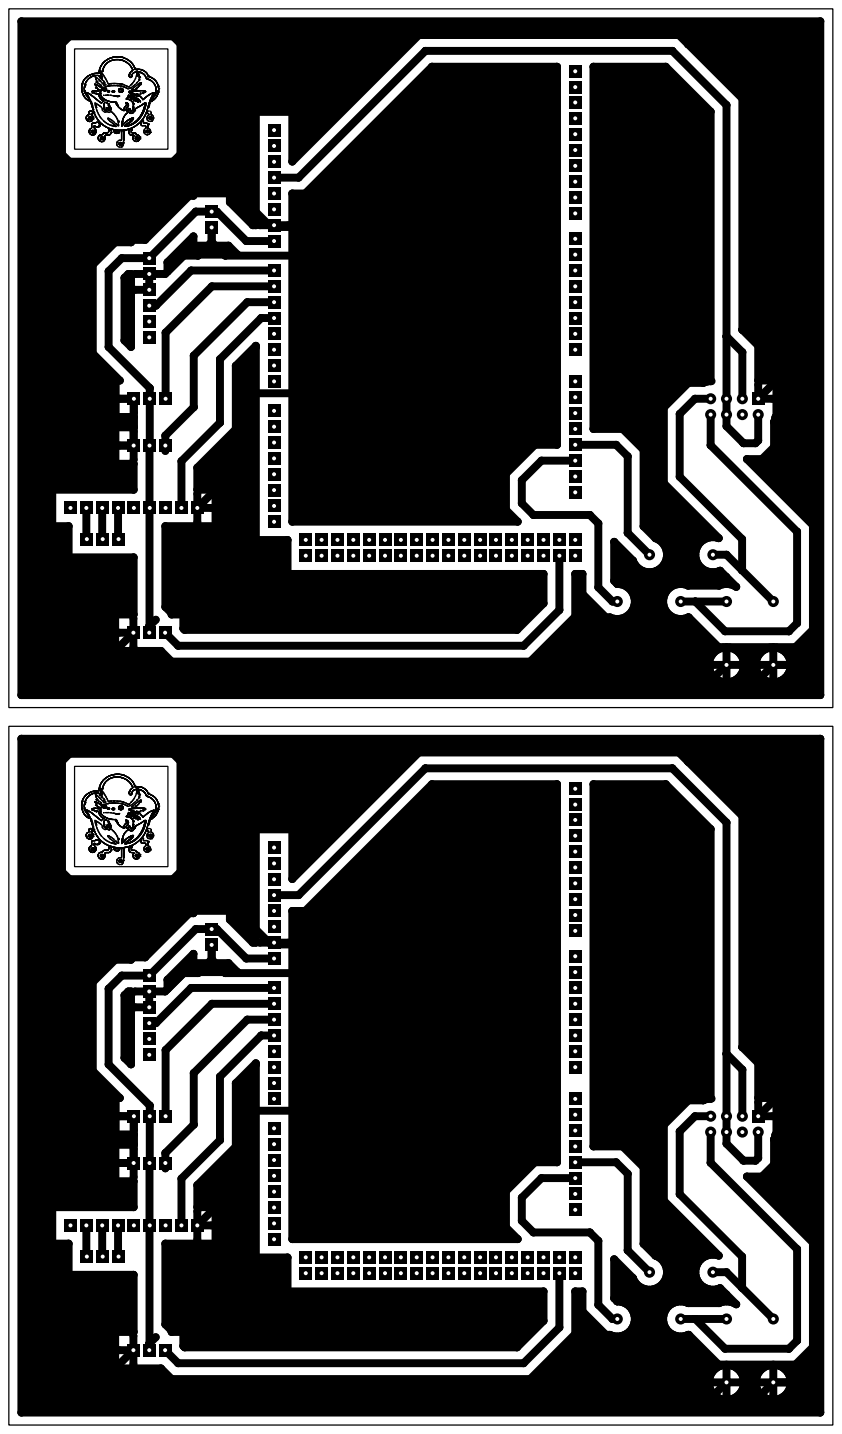
[picture p80: page 1]
