Acidjeremy07/Monitoreo-Ambystomas-Arduino/PCB/tt-v7.PDF

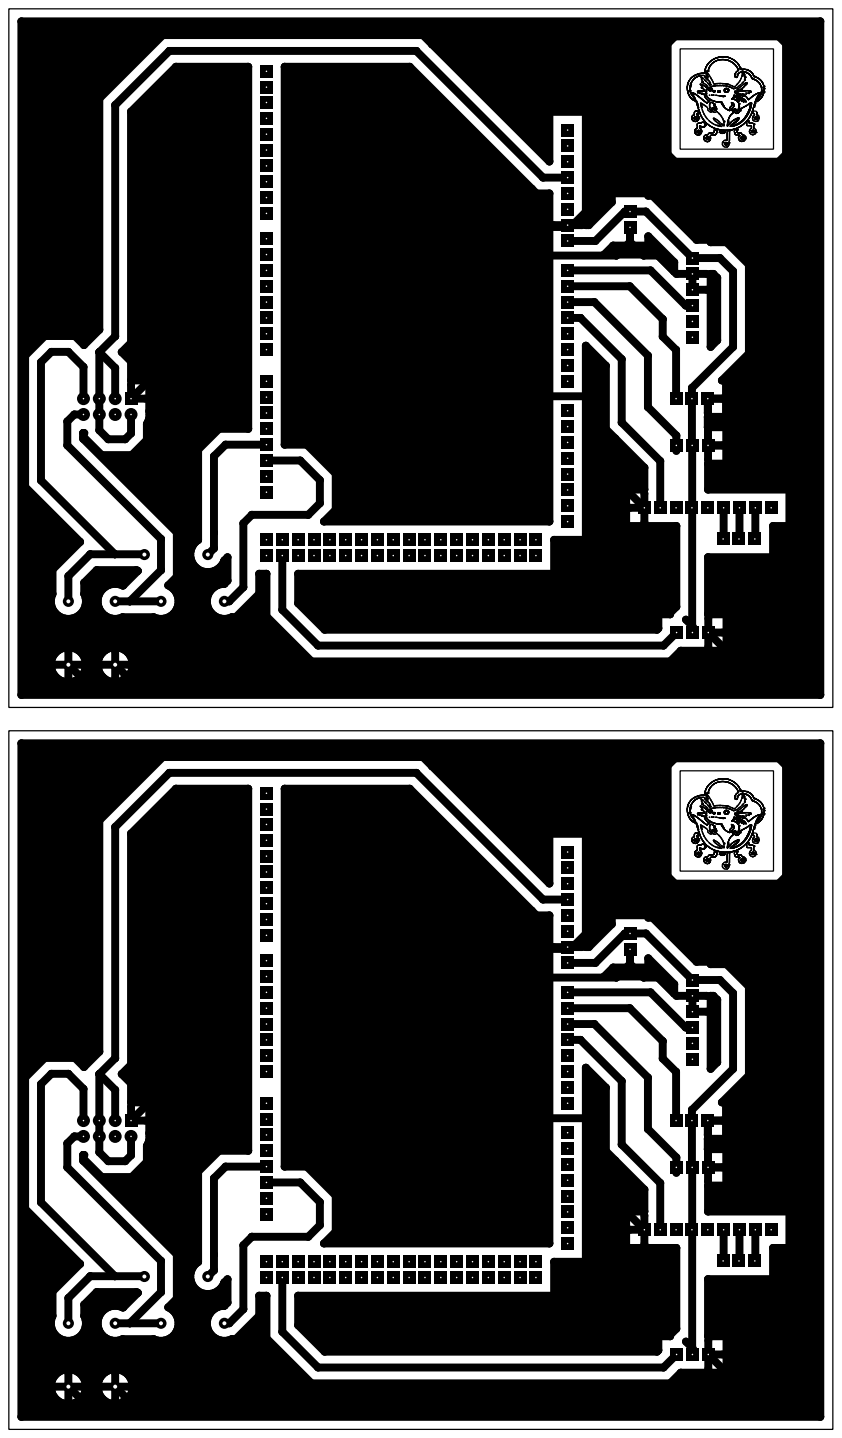
[picture p81: page 1]
