Acidjeremy07/Monitoreo-Ambystomas-Arduino/PCB/PDF imprimir/TT Ambystoma v2.PDF

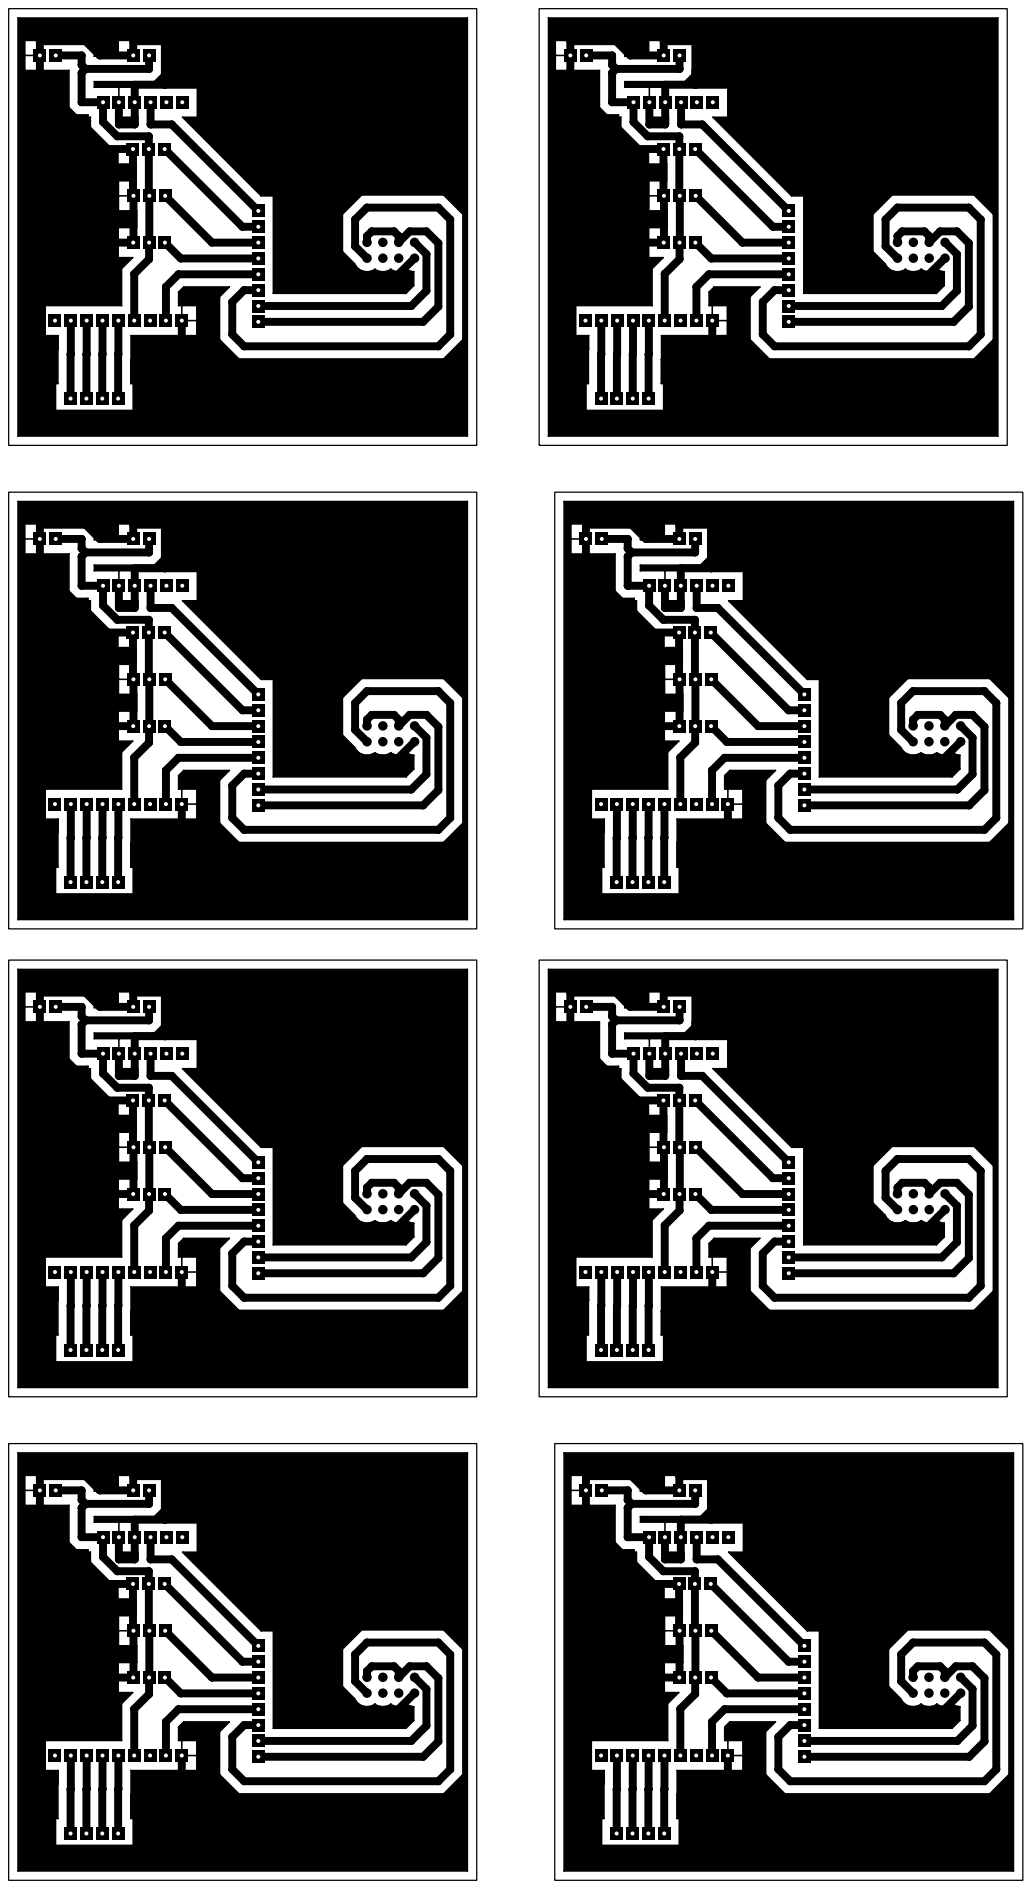
[picture p82: page 1]
